massengineer/FYP-ML-Bird-Scarer/train_data_for_fifth_model/train_batch1262.jpg

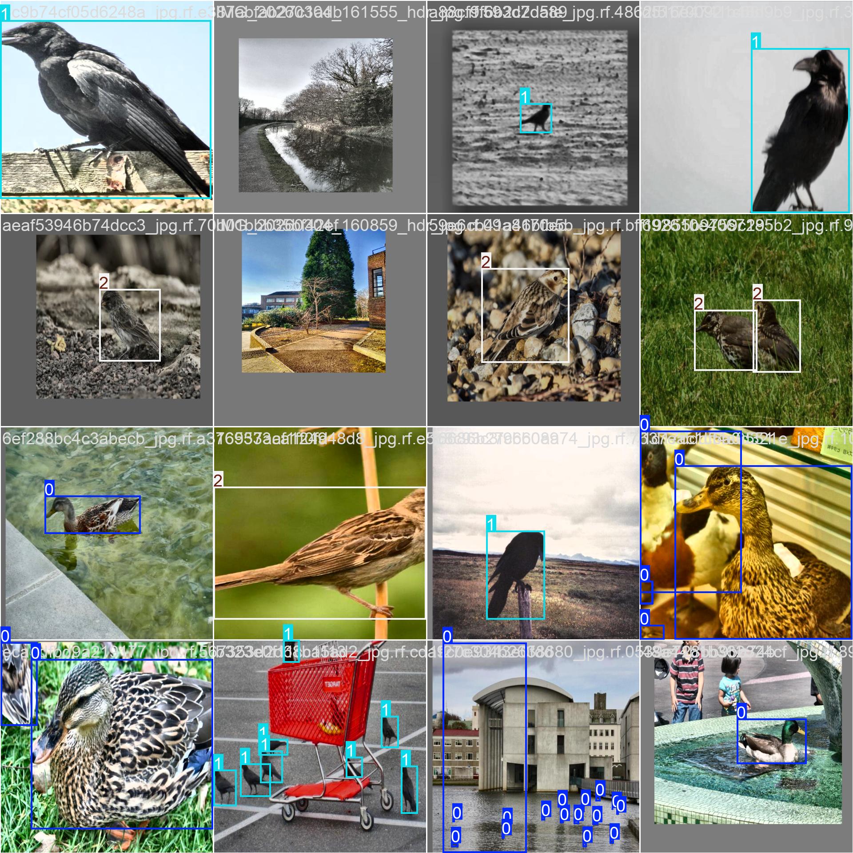
train_data_for_fifth_model/train_batch1262.jpg
