massengineer/FYP-ML-Bird-Scarer/train_data_for_first_model/train_batch451.jpg

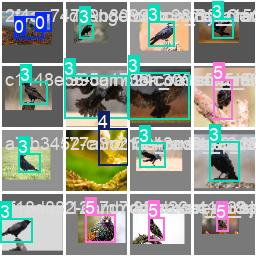
train_data_for_first_model/train_batch451.jpg
