massengineer/FYP-ML-Bird-Scarer/train_data_for_first_model/train_batch452.jpg

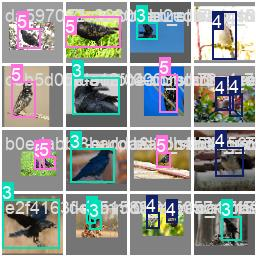
train_data_for_first_model/train_batch452.jpg
