massengineer/FYP-ML-Bird-Scarer/train_data_for_second_model/train_batch12731.jpg

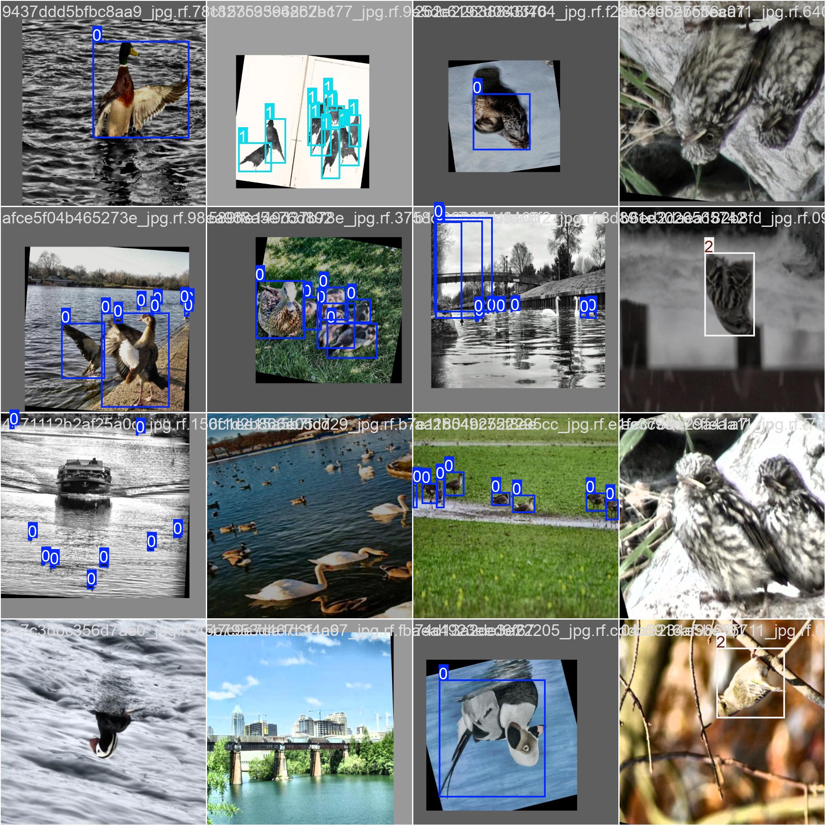
train_data_for_second_model/train_batch12731.jpg
