massengineer/FYP-ML-Bird-Scarer/train_data_for_second_model/val_batch2_labels.jpg

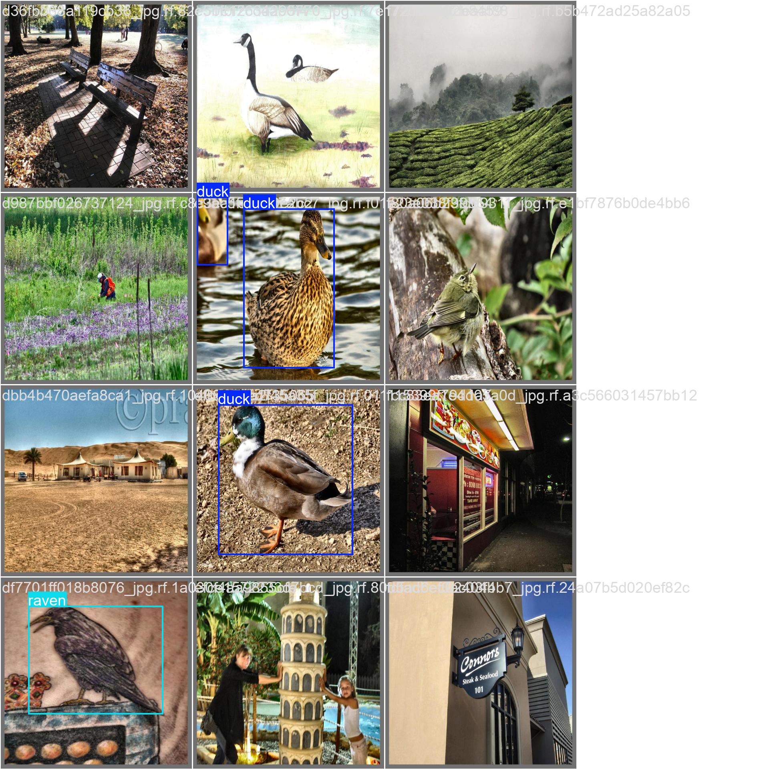
train_data_for_second_model/val_batch2_labels.jpg
