massengineer/FYP-ML-Bird-Scarer/train_data_for_sixth_model/BoxF1_curve.png

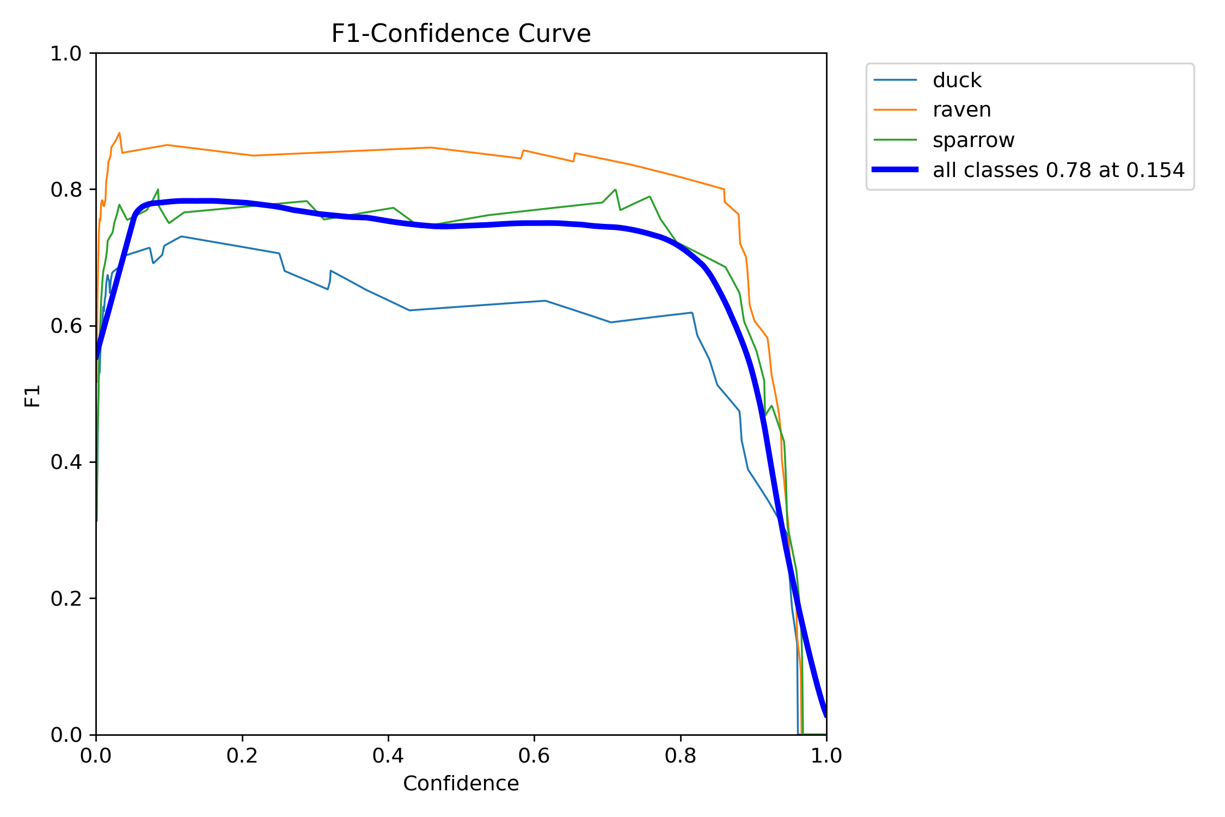
train_data_for_sixth_model/BoxF1_curve.png
