massengineer/FYP-ML-Bird-Scarer/train_data_for_sixth_model/confusion_matrix.png

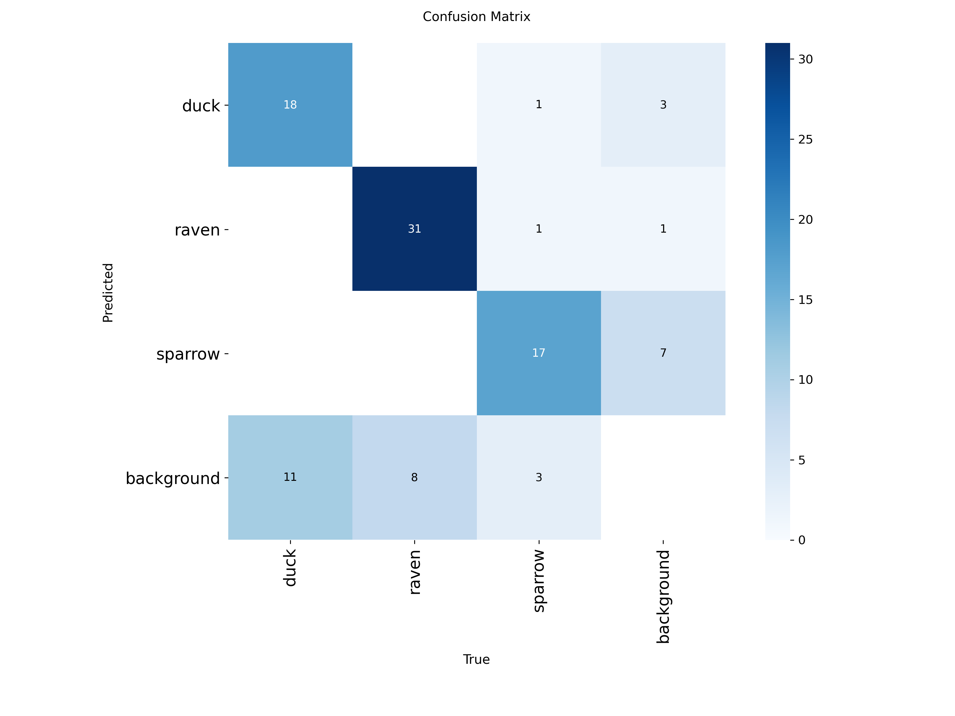
train_data_for_sixth_model/confusion_matrix.png
