massengineer/FYP-ML-Bird-Scarer/train_data_for_sixth_model/confusion_matrix_normalized.png

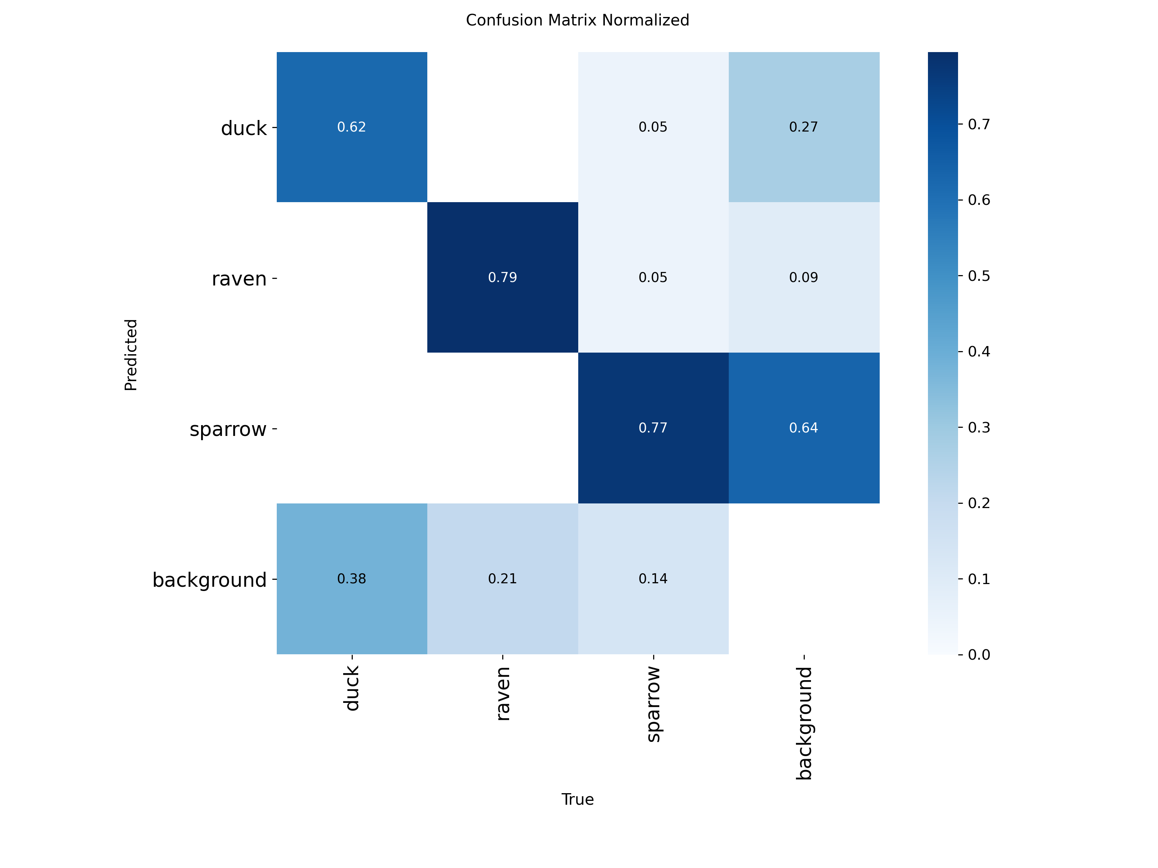
train_data_for_sixth_model/confusion_matrix_normalized.png
