massengineer/FYP-ML-Bird-Scarer/train_data_for_sixth_model/labels.jpg

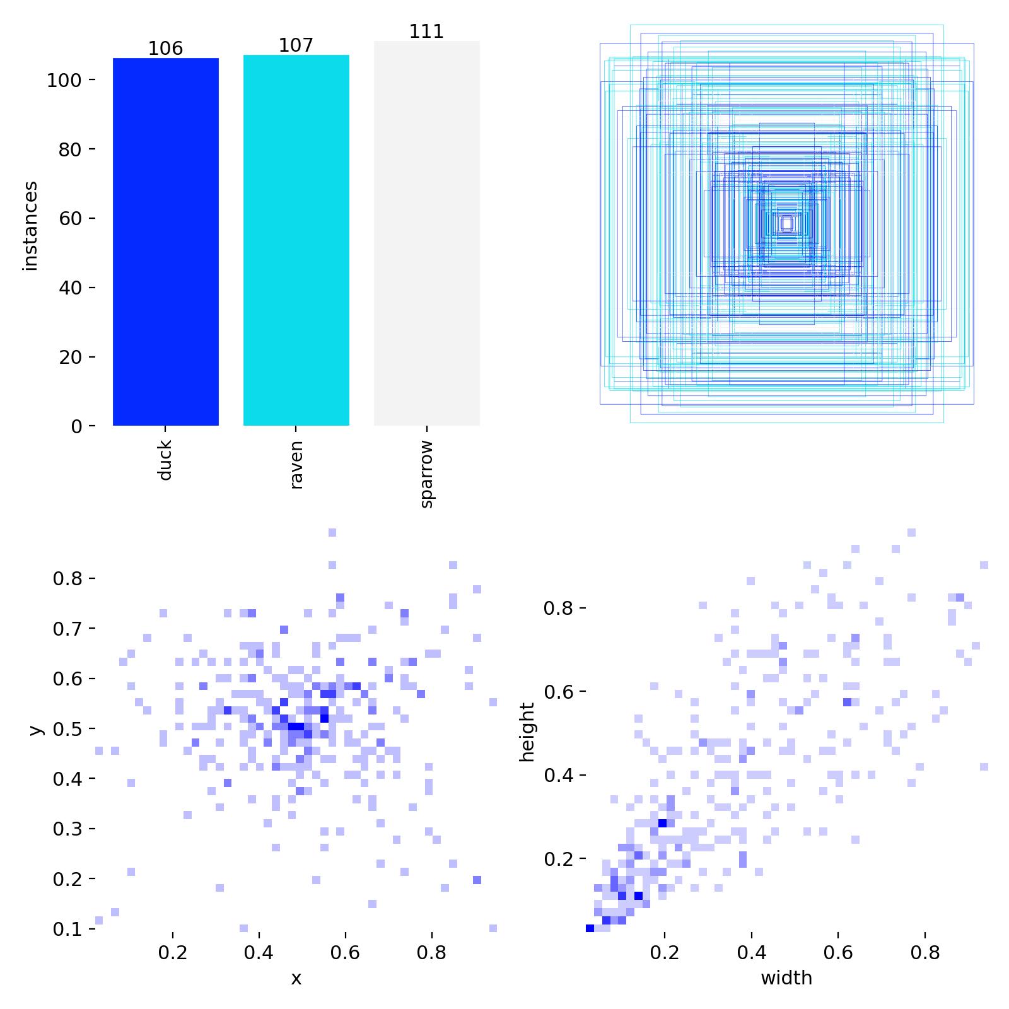
train_data_for_sixth_model/labels.jpg
