massengineer/FYP-ML-Bird-Scarer/train_data_for_sixth_model/train_batch1122.jpg

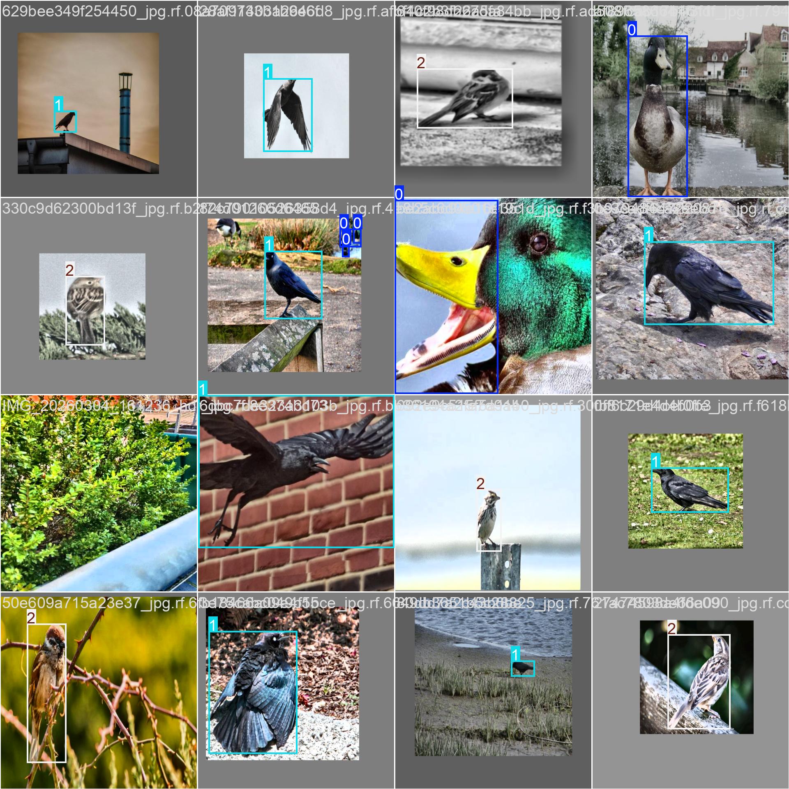
train_data_for_sixth_model/train_batch1122.jpg
