massengineer/FYP-ML-Bird-Scarer/train_data_for_sixth_model/val_batch1_labels.jpg

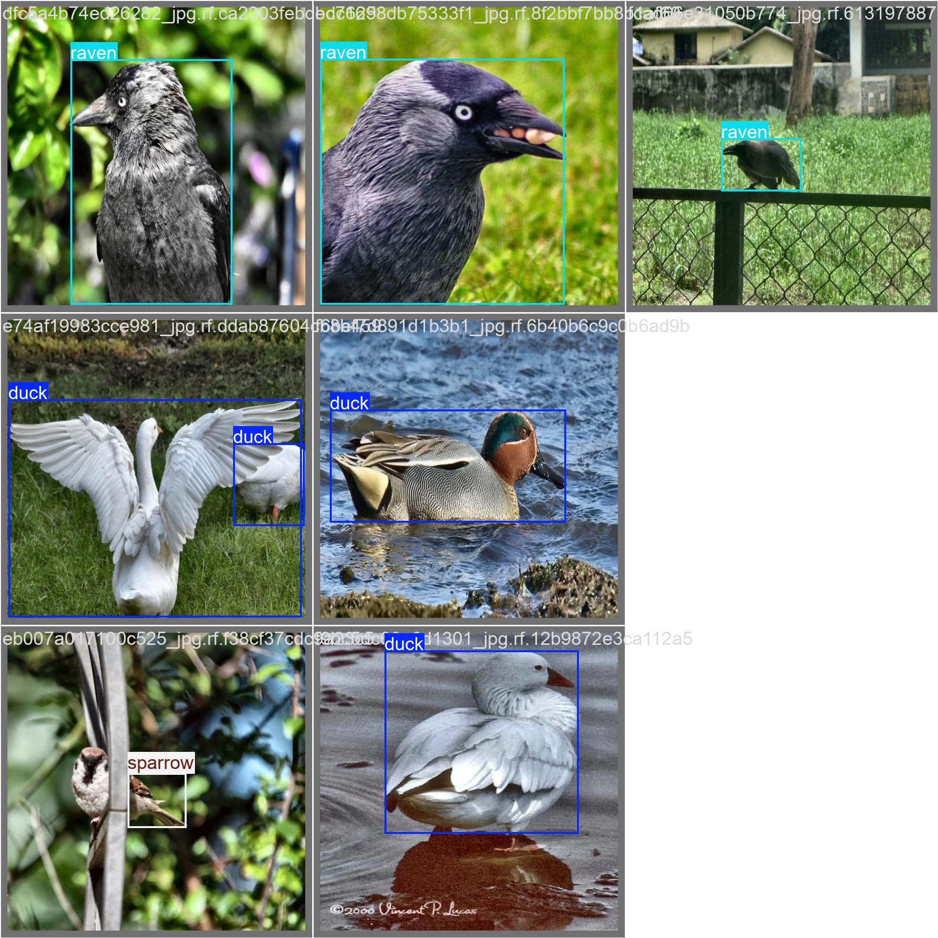
train_data_for_sixth_model/val_batch1_labels.jpg
