massengineer/FYP-ML-Bird-Scarer/train_data_for_third_model/train_batch13490.jpg

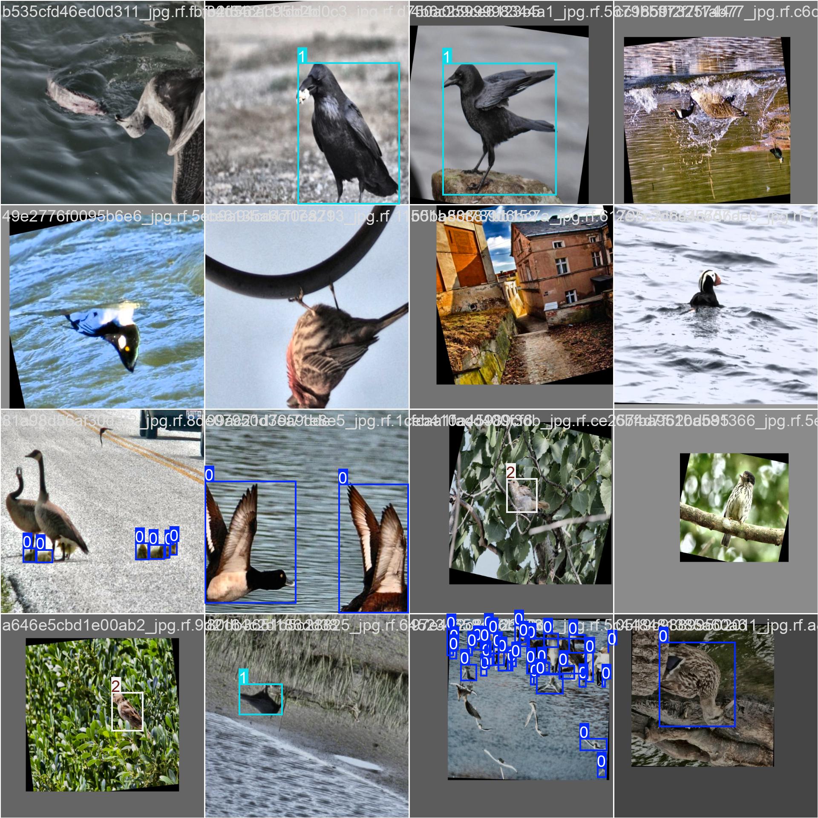
train_data_for_third_model/train_batch13490.jpg
