massengineer/FYP-ML-Bird-Scarer/train_data_for_third_model/train_batch13491.jpg

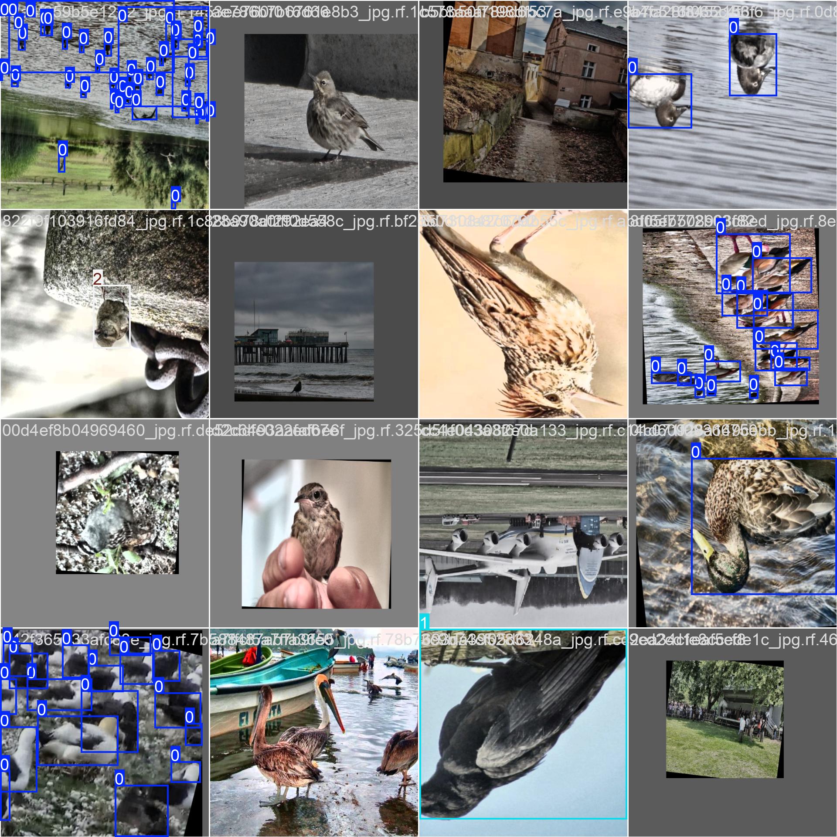
train_data_for_third_model/train_batch13491.jpg
