massengineer/FYP-ML-Bird-Scarer/train_data_for_third_model/train_batch13492.jpg

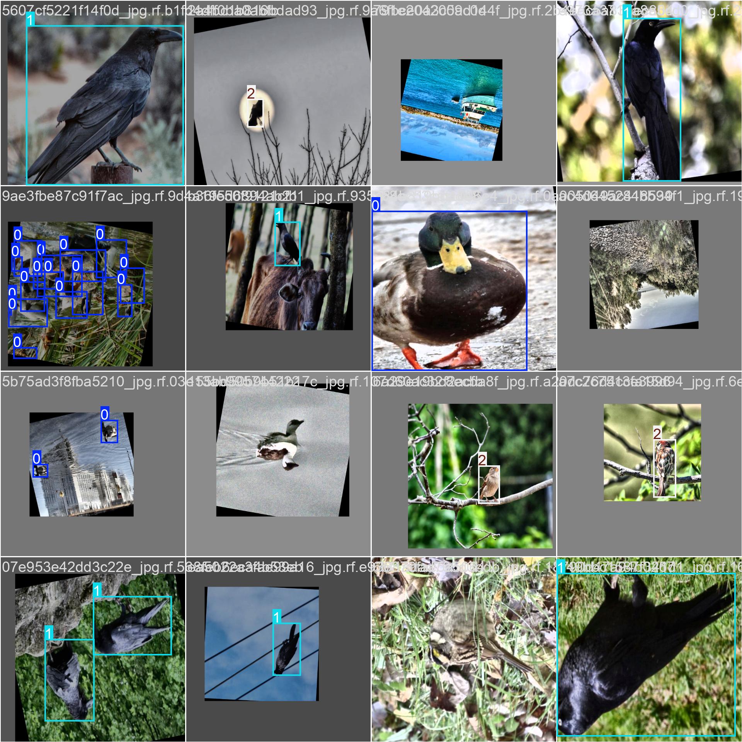
train_data_for_third_model/train_batch13492.jpg
