massengineer/FYP-ML-Bird-Scarer/train_data_for_third_model/val_batch2_labels.jpg

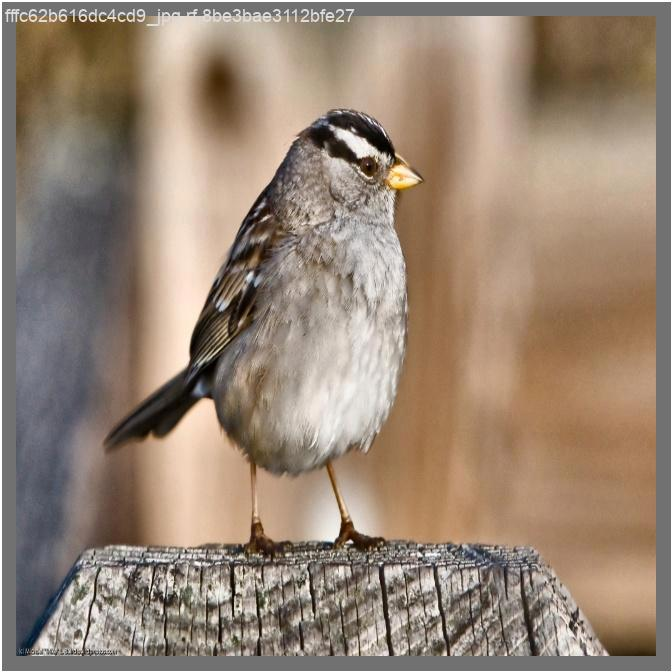
train_data_for_third_model/val_batch2_labels.jpg
