massengineer/FYP-ML-Bird-Scarer/yolo_datasets/raw_datasets/raw_backgrounds_for_fourth_model/IMG_20260304_160844_hdr.jpg

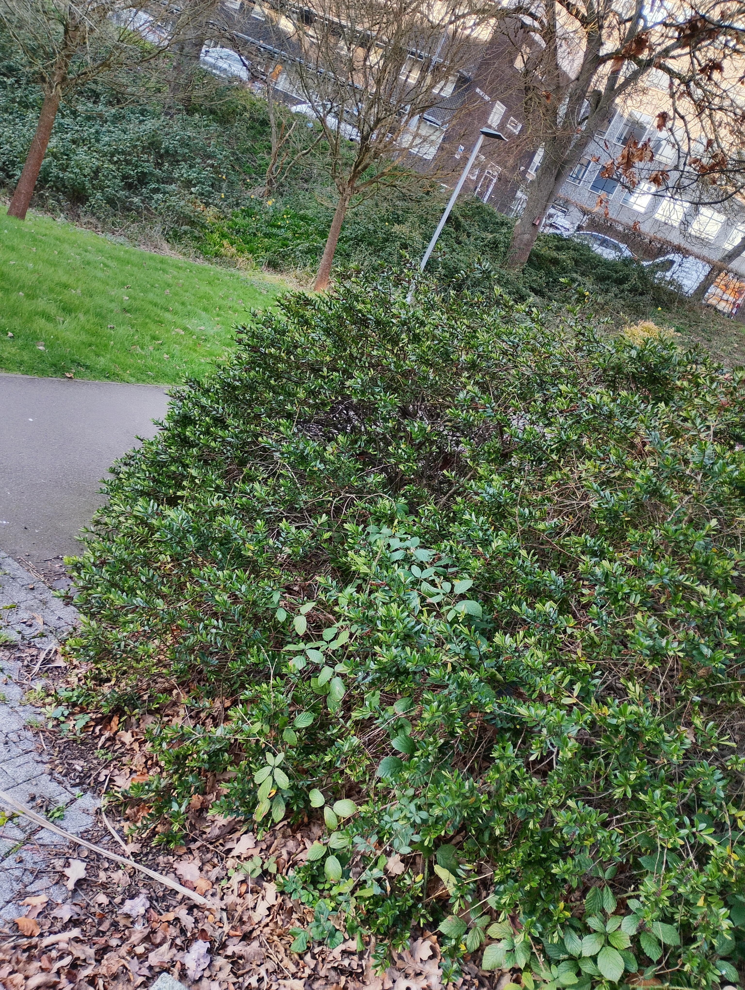
yolo_datasets/raw_datasets/raw_backgrounds_for_fourth_model/IMG_20260304_160844_hdr.jpg
