massengineer/FYP-ML-Bird-Scarer/fifth_model_validation_images/images/0be64d0484da7f5d_jpg.rf.04b6d1586df6ac3ba64640923855f992.jpg

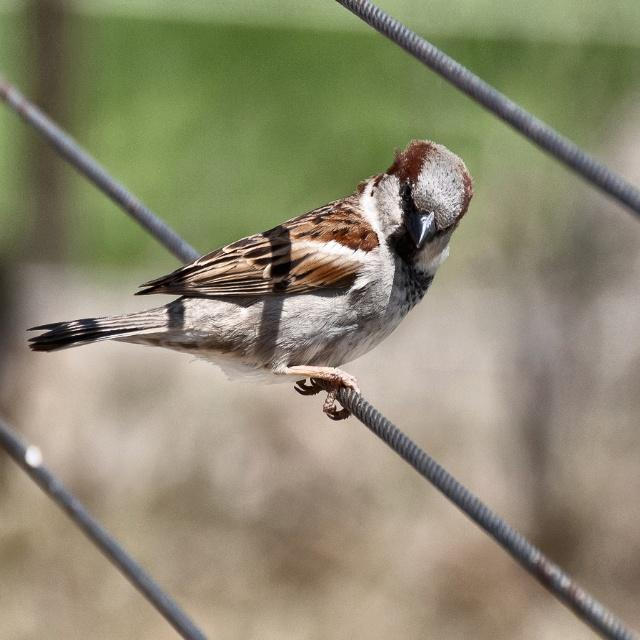
fifth_model_validation_images/images/0be64d0484da7f5d_jpg.rf.04b6d1586df6ac3ba64640923855f992.jpg
