massengineer/FYP-ML-Bird-Scarer/fifth_model_validation_images/images/0de4b4a7943ed37f_jpg.rf.b9594d37234d768218a4663b704f7083.jpg

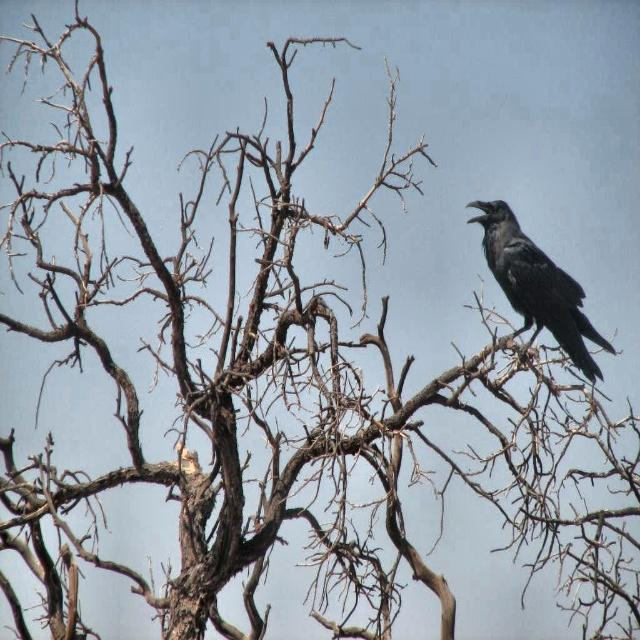
fifth_model_validation_images/images/0de4b4a7943ed37f_jpg.rf.b9594d37234d768218a4663b704f7083.jpg
