massengineer/FYP-ML-Bird-Scarer/fifth_model_validation_images/images/0f1b6b456ff8cd9d_jpg.rf.248c24bbcdb2682d79712362b7e4eebd.jpg

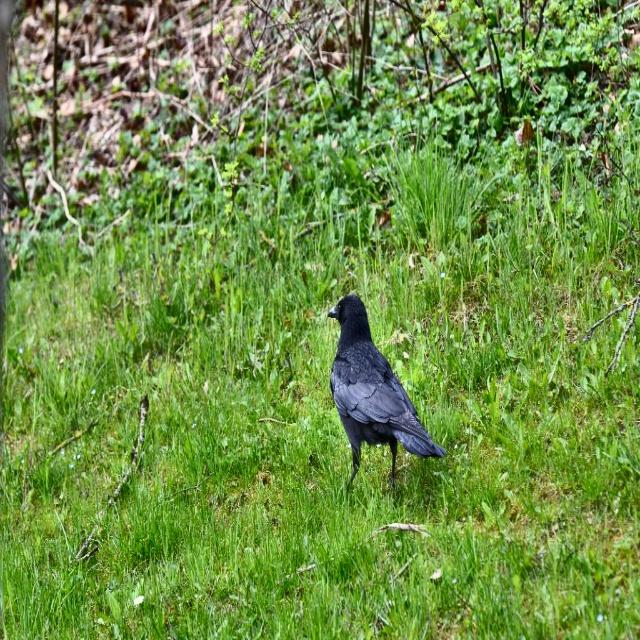
fifth_model_validation_images/images/0f1b6b456ff8cd9d_jpg.rf.248c24bbcdb2682d79712362b7e4eebd.jpg
