massengineer/FYP-ML-Bird-Scarer/fifth_model_validation_images/images/1dcef06e49ea7a7c_jpg.rf.42e672c7e4f9906fecd4efd1ddf9af88.jpg

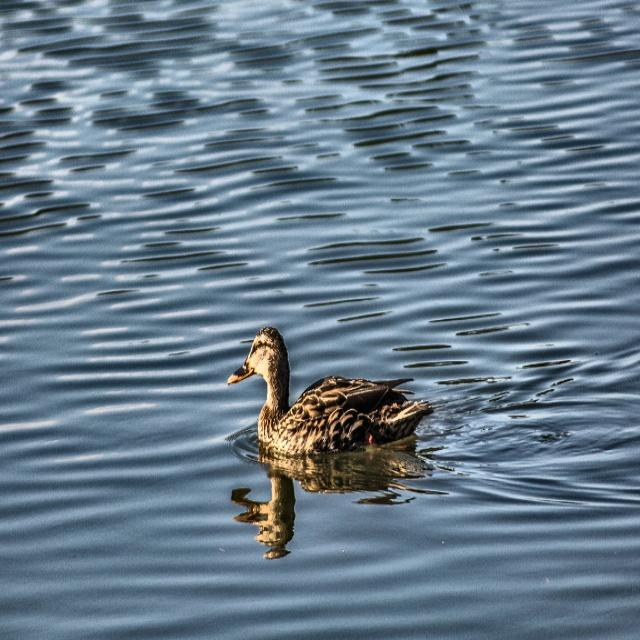
fifth_model_validation_images/images/1dcef06e49ea7a7c_jpg.rf.42e672c7e4f9906fecd4efd1ddf9af88.jpg
