massengineer/FYP-ML-Bird-Scarer/fifth_model_validation_images/images/2b569ea590ce1db2_jpg.rf.67d2292251b5af2b555186cf5ea705ad.jpg

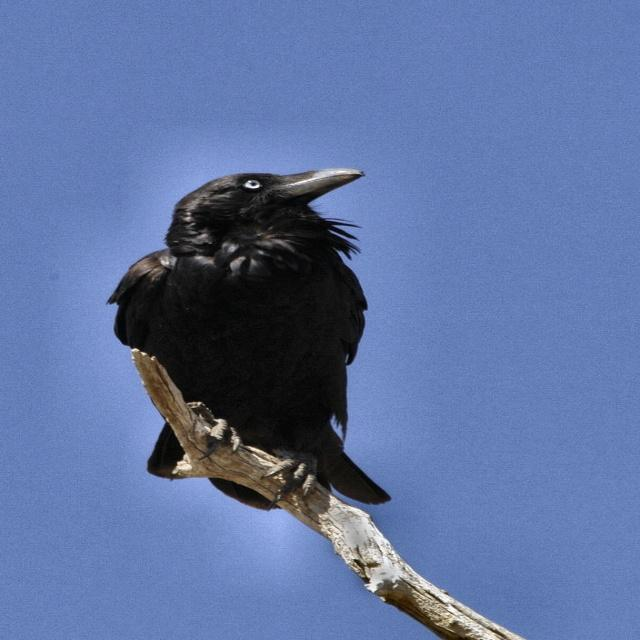
fifth_model_validation_images/images/2b569ea590ce1db2_jpg.rf.67d2292251b5af2b555186cf5ea705ad.jpg
