massengineer/FYP-ML-Bird-Scarer/fifth_model_validation_images/images/2d2721cced07626c_jpg.rf.696016c7bf0ef4f652db7f2fa16d3ebe.jpg

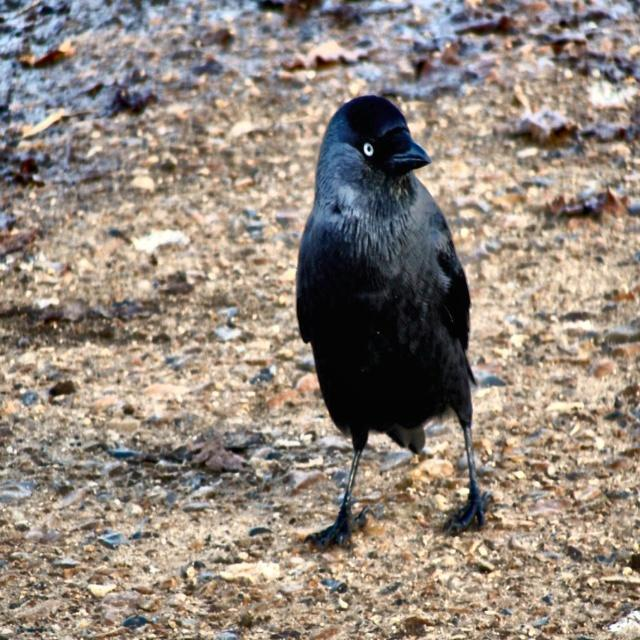
fifth_model_validation_images/images/2d2721cced07626c_jpg.rf.696016c7bf0ef4f652db7f2fa16d3ebe.jpg
