massengineer/FYP-ML-Bird-Scarer/fifth_model_validation_images/images/2de9d305609b8cc4_jpg.rf.c2fc4baab4b9f6159f9ddb58a70e6da2.jpg

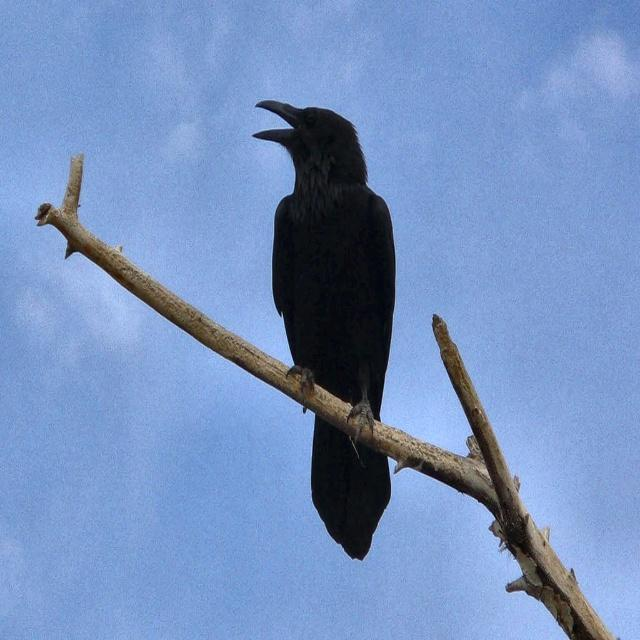
fifth_model_validation_images/images/2de9d305609b8cc4_jpg.rf.c2fc4baab4b9f6159f9ddb58a70e6da2.jpg
