massengineer/FYP-ML-Bird-Scarer/fifth_model_validation_images/images/3c0b50f20b9cccb5_jpg.rf.caedc038e160330f41f902fb228554f5.jpg

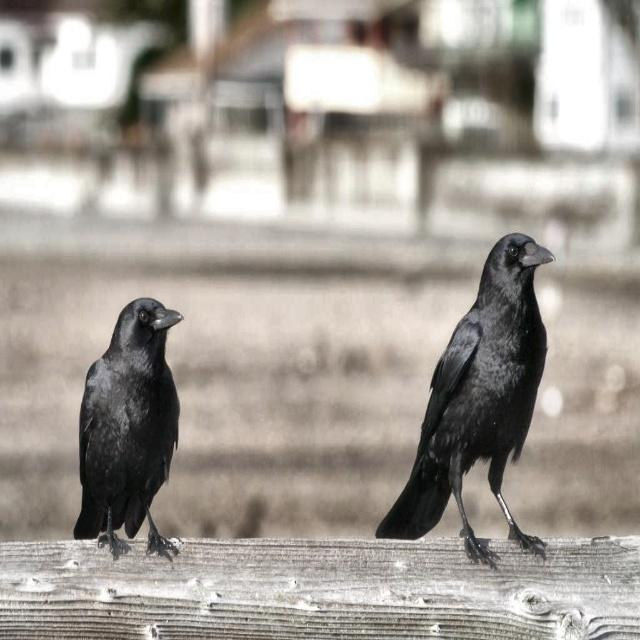
fifth_model_validation_images/images/3c0b50f20b9cccb5_jpg.rf.caedc038e160330f41f902fb228554f5.jpg
