massengineer/FYP-ML-Bird-Scarer/fifth_model_validation_images/images/3c9103fa934be876_jpg.rf.1b80672a4a2a1a34eb28aad57273ca6f.jpg

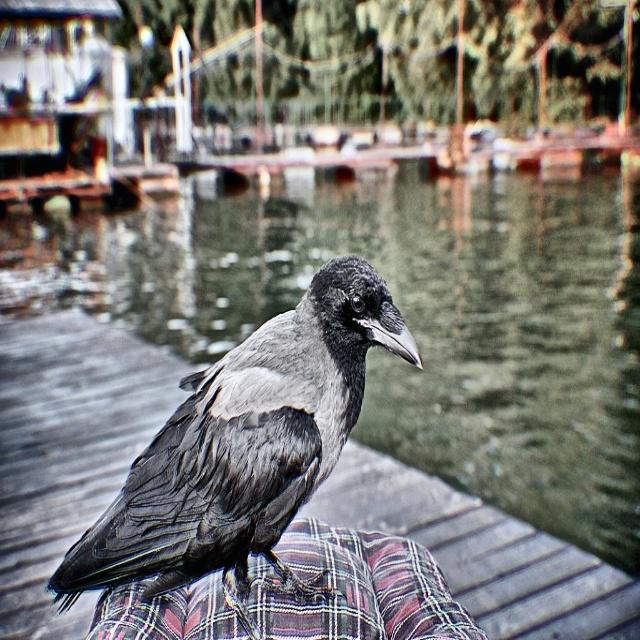
fifth_model_validation_images/images/3c9103fa934be876_jpg.rf.1b80672a4a2a1a34eb28aad57273ca6f.jpg
