massengineer/FYP-ML-Bird-Scarer/fifth_model_validation_images/images/3ce8491f37576abe_jpg.rf.4be57851d7a430a2213e9c7240d35ce1.jpg

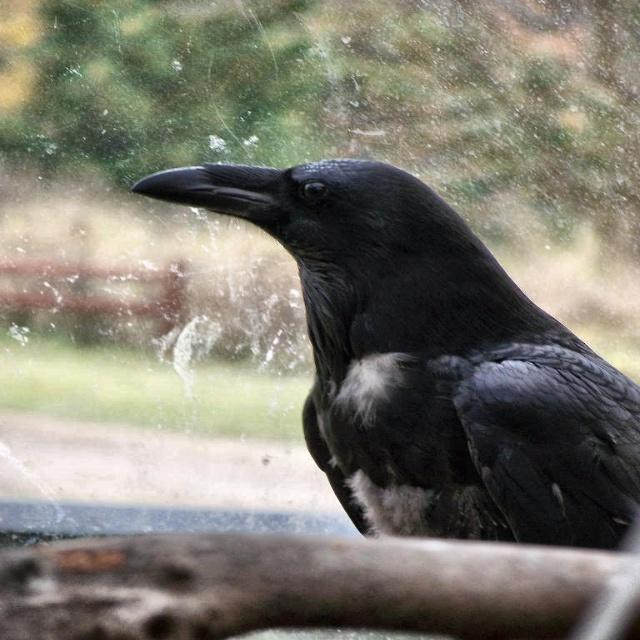
fifth_model_validation_images/images/3ce8491f37576abe_jpg.rf.4be57851d7a430a2213e9c7240d35ce1.jpg
