massengineer/FYP-ML-Bird-Scarer/fifth_model_validation_images/images/4ac98103f6902418_jpg.rf.f355e2eece73f3efba47b437c8df5437.jpg

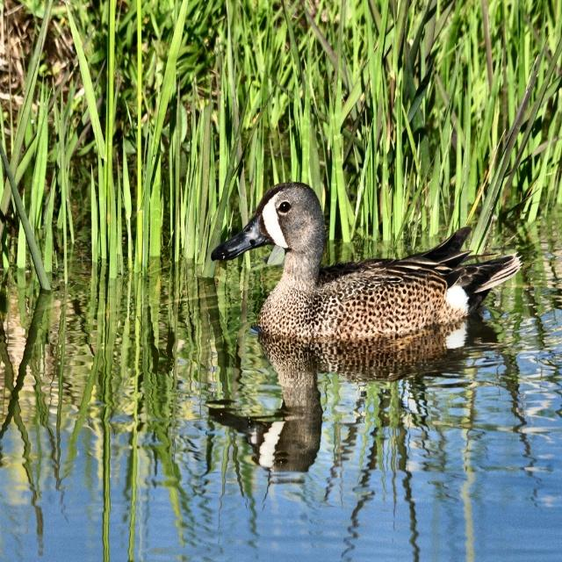
fifth_model_validation_images/images/4ac98103f6902418_jpg.rf.f355e2eece73f3efba47b437c8df5437.jpg
