massengineer/FYP-ML-Bird-Scarer/fifth_model_validation_images/images/4cb8bc5a7666f66f_jpg.rf.4776c85a03ee199fc77abfe076986128.jpg

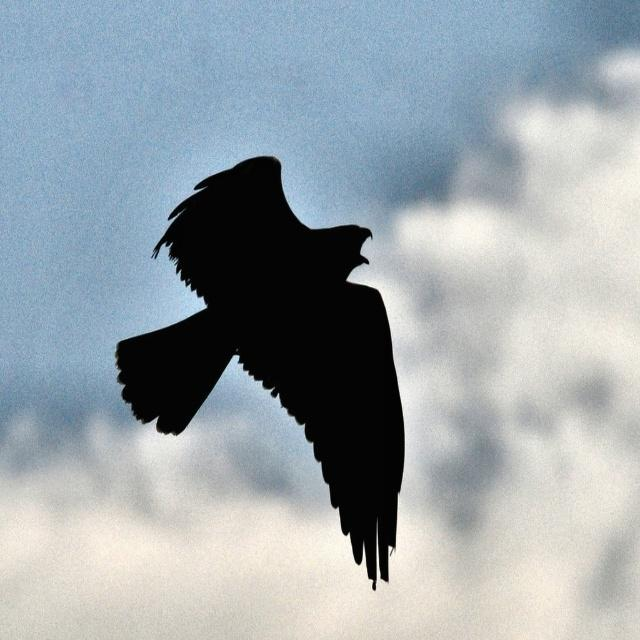
fifth_model_validation_images/images/4cb8bc5a7666f66f_jpg.rf.4776c85a03ee199fc77abfe076986128.jpg
