massengineer/FYP-ML-Bird-Scarer/fifth_model_validation_images/images/4effb07ed2c22bd3_jpg.rf.99be9b13471a686662674c35d63af22f.jpg

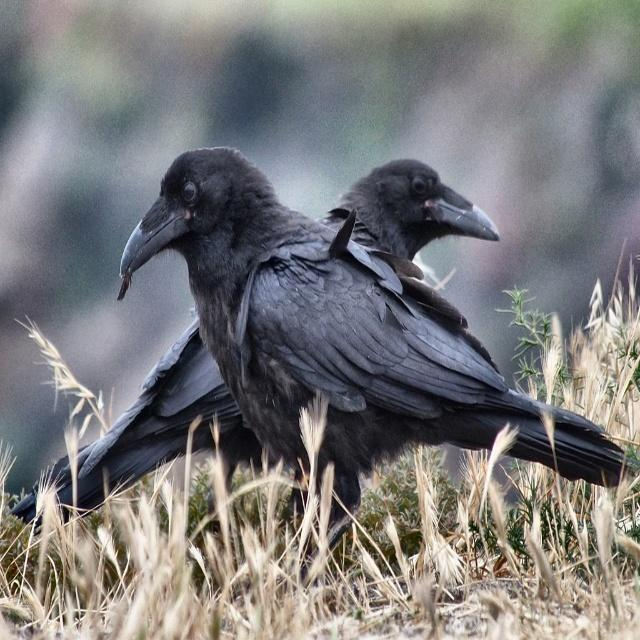
fifth_model_validation_images/images/4effb07ed2c22bd3_jpg.rf.99be9b13471a686662674c35d63af22f.jpg
