massengineer/FYP-ML-Bird-Scarer/fifth_model_validation_images/images/5e3f348764a5eef8_jpg.rf.422f0adb134aaac1838261bf152511c6.jpg

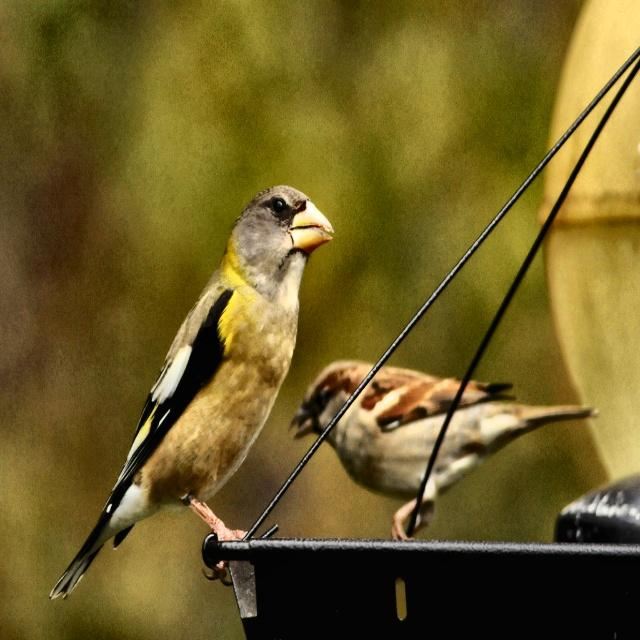
fifth_model_validation_images/images/5e3f348764a5eef8_jpg.rf.422f0adb134aaac1838261bf152511c6.jpg
