massengineer/FYP-ML-Bird-Scarer/fifth_model_validation_images/images/5fa36b7ab3f99b57_jpg.rf.4fb009745905087155a14afa6f6e8ed5.jpg

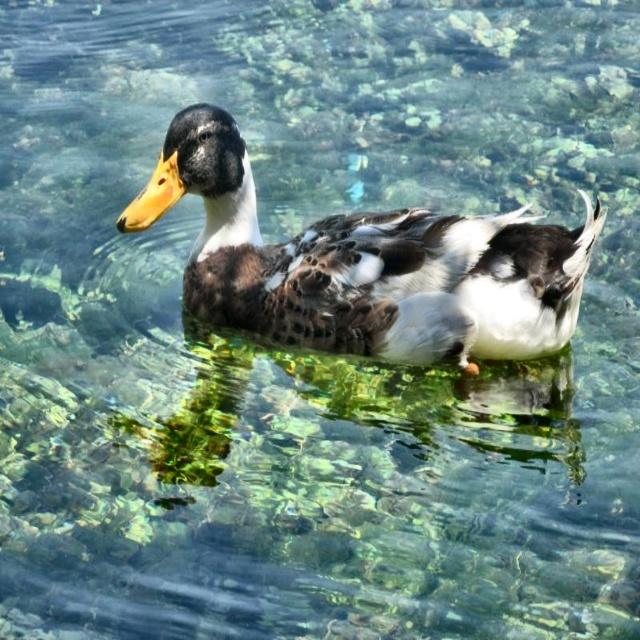
fifth_model_validation_images/images/5fa36b7ab3f99b57_jpg.rf.4fb009745905087155a14afa6f6e8ed5.jpg
