massengineer/FYP-ML-Bird-Scarer/fifth_model_validation_images/images/7e1ffb219a2a522b_jpg.rf.1393dfc984291c2c9076b45750de1e1d.jpg

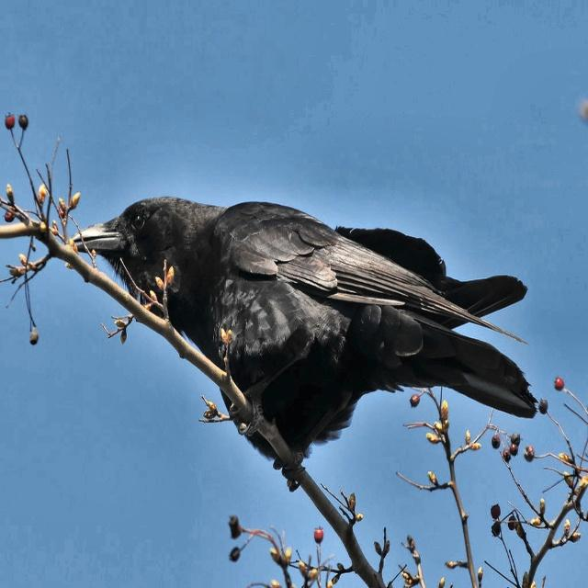
fifth_model_validation_images/images/7e1ffb219a2a522b_jpg.rf.1393dfc984291c2c9076b45750de1e1d.jpg
