massengineer/FYP-ML-Bird-Scarer/fifth_model_validation_images/images/8bce0ef025411ed1_jpg.rf.2814e396186e43bf01ed99291d027d92.jpg

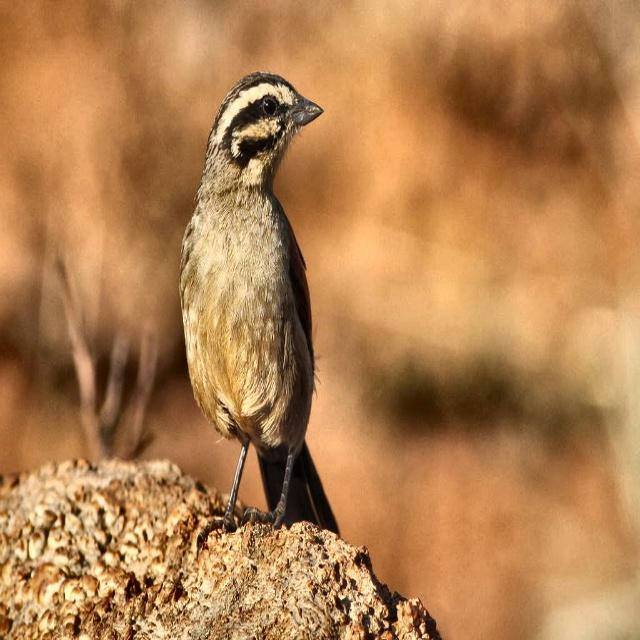
fifth_model_validation_images/images/8bce0ef025411ed1_jpg.rf.2814e396186e43bf01ed99291d027d92.jpg
