massengineer/FYP-ML-Bird-Scarer/fifth_model_validation_images/images/9bb2d29bb96724c6_jpg.rf.1a6e348eabfad239e67b68433f5f388f.jpg

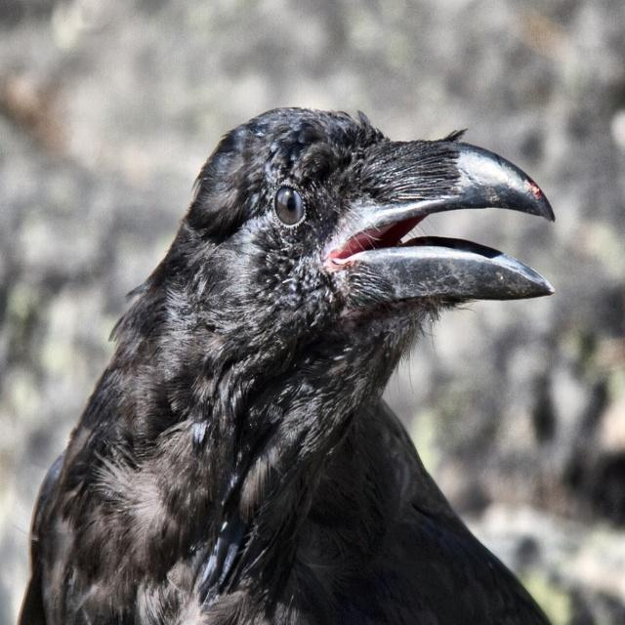
fifth_model_validation_images/images/9bb2d29bb96724c6_jpg.rf.1a6e348eabfad239e67b68433f5f388f.jpg
