massengineer/FYP-ML-Bird-Scarer/fifth_model_validation_images/images/9f813f146b94f087_jpg.rf.ed6a436854f7ce6db7ea7519b66a86ef.jpg

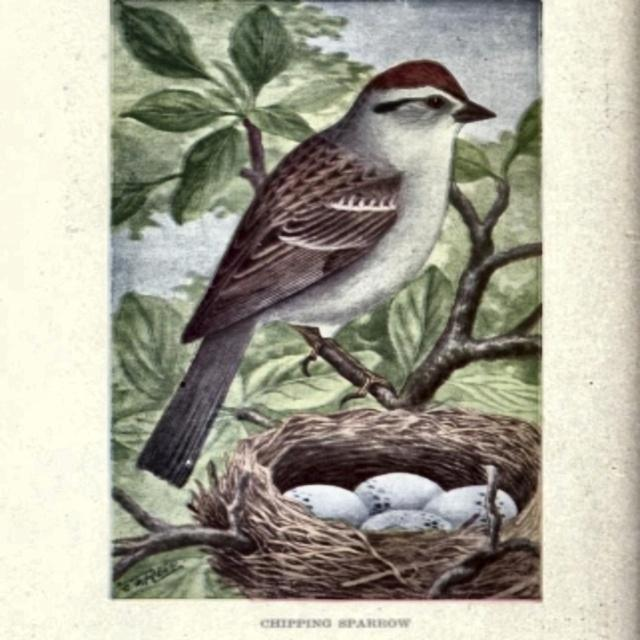
fifth_model_validation_images/images/9f813f146b94f087_jpg.rf.ed6a436854f7ce6db7ea7519b66a86ef.jpg
