massengineer/FYP-ML-Bird-Scarer/fifth_model_validation_images/images/22aa6924c696b9df_jpg.rf.54d9e55d646cb2611108bd9d270b6c9e.jpg

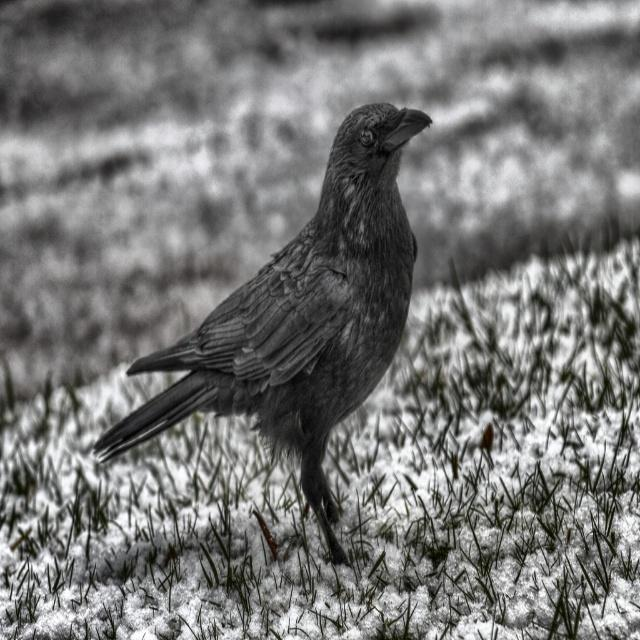
fifth_model_validation_images/images/22aa6924c696b9df_jpg.rf.54d9e55d646cb2611108bd9d270b6c9e.jpg
