massengineer/FYP-ML-Bird-Scarer/fifth_model_validation_images/images/24cab1cdcadd2906_jpg.rf.8a631ed6f84598b9b1aee93e4d02c651.jpg

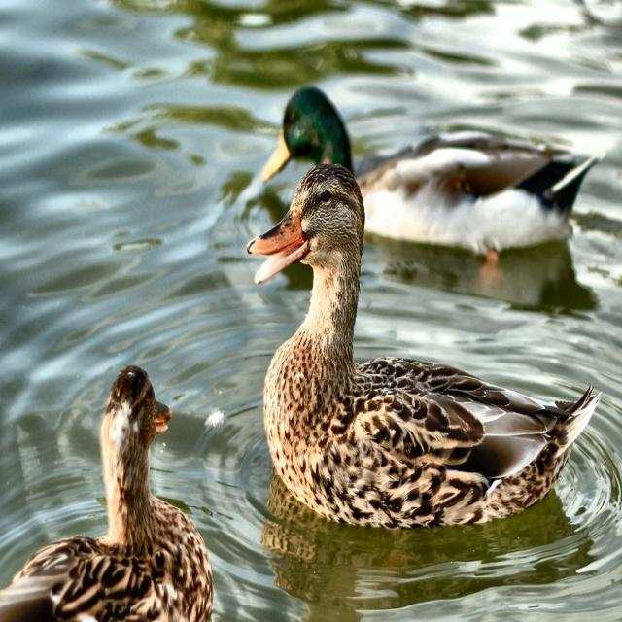
fifth_model_validation_images/images/24cab1cdcadd2906_jpg.rf.8a631ed6f84598b9b1aee93e4d02c651.jpg
