massengineer/FYP-ML-Bird-Scarer/fifth_model_validation_images/images/057f0de7e671b75c_jpg.rf.2dd9f41e60b7a2de076f6edf6c3f98c5.jpg

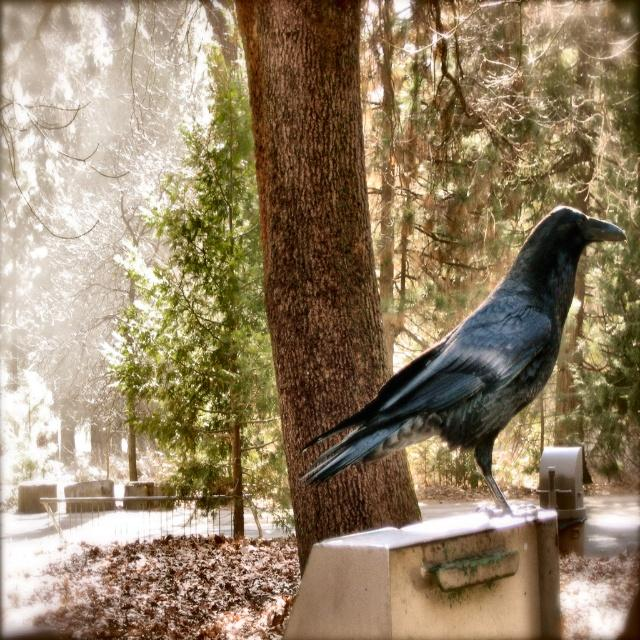
fifth_model_validation_images/images/057f0de7e671b75c_jpg.rf.2dd9f41e60b7a2de076f6edf6c3f98c5.jpg
