massengineer/FYP-ML-Bird-Scarer/fifth_model_validation_images/images/73a1b642339b4ec0_jpg.rf.175f9d27eda6b595fa8adb0b344427a3.jpg

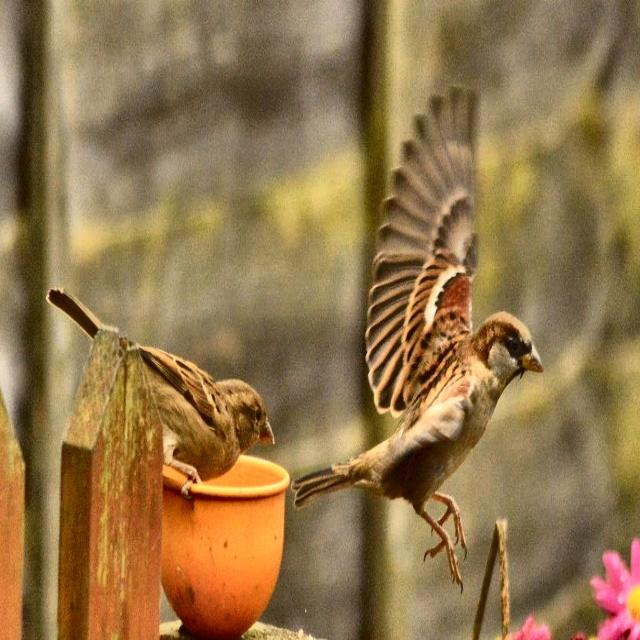
fifth_model_validation_images/images/73a1b642339b4ec0_jpg.rf.175f9d27eda6b595fa8adb0b344427a3.jpg
