massengineer/FYP-ML-Bird-Scarer/fifth_model_validation_images/images/84ef1881685cd206_jpg.rf.76c47fa663c3859b4896b602b45732bb.jpg

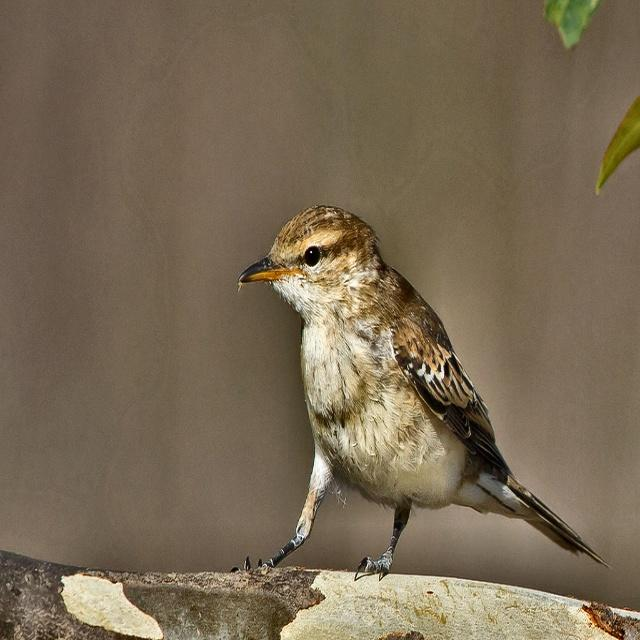
fifth_model_validation_images/images/84ef1881685cd206_jpg.rf.76c47fa663c3859b4896b602b45732bb.jpg
