massengineer/FYP-ML-Bird-Scarer/fifth_model_validation_images/images/93b6f17a0cf6b67b_jpg.rf.c7610ac2f88afec8820649ae66cb56ca.jpg

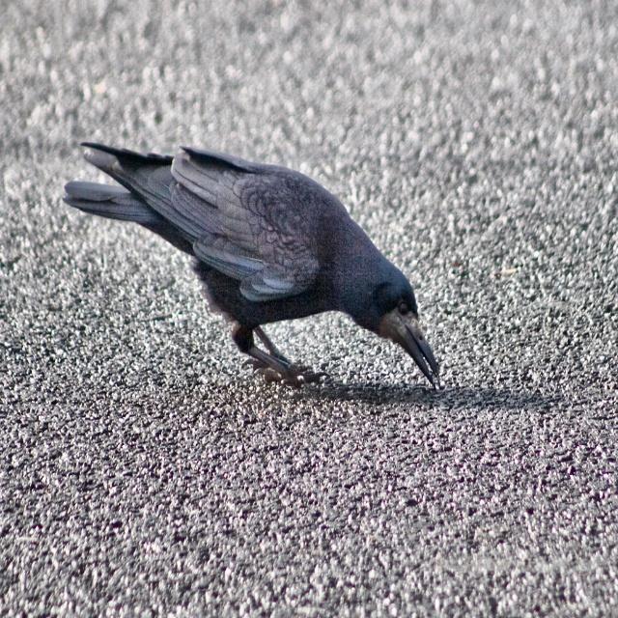
fifth_model_validation_images/images/93b6f17a0cf6b67b_jpg.rf.c7610ac2f88afec8820649ae66cb56ca.jpg
