massengineer/FYP-ML-Bird-Scarer/fifth_model_validation_images/images/94eb81cf26257bfb_jpg.rf.2ae2b793689980e837b499f0b69c3a8b.jpg

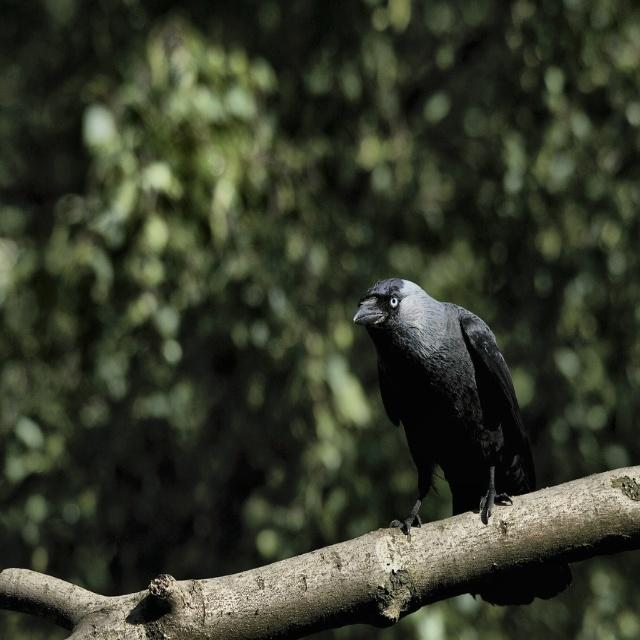
fifth_model_validation_images/images/94eb81cf26257bfb_jpg.rf.2ae2b793689980e837b499f0b69c3a8b.jpg
