massengineer/FYP-ML-Bird-Scarer/fifth_model_validation_images/images/97c735f24d1822c4_jpg.rf.b55590020fa06321282a1aeb94cfc051.jpg

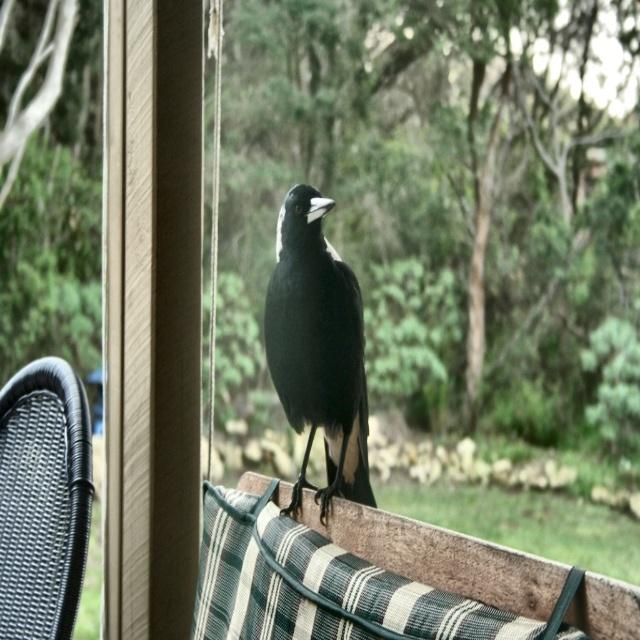
fifth_model_validation_images/images/97c735f24d1822c4_jpg.rf.b55590020fa06321282a1aeb94cfc051.jpg
