massengineer/FYP-ML-Bird-Scarer/fifth_model_validation_images/images/99d4241ec2013bb5_jpg.rf.05ae8fb1f897e008a1f890e7e9f91ab8.jpg

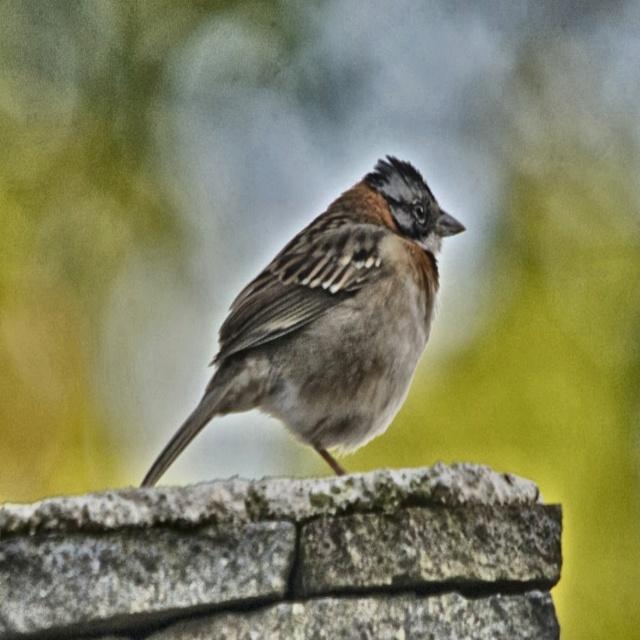
fifth_model_validation_images/images/99d4241ec2013bb5_jpg.rf.05ae8fb1f897e008a1f890e7e9f91ab8.jpg
