massengineer/FYP-ML-Bird-Scarer/fifth_model_validation_images/images/454ffdabe8fc2a90_jpg.rf.b0b41fb94497174f44b9e8e404c59a25.jpg

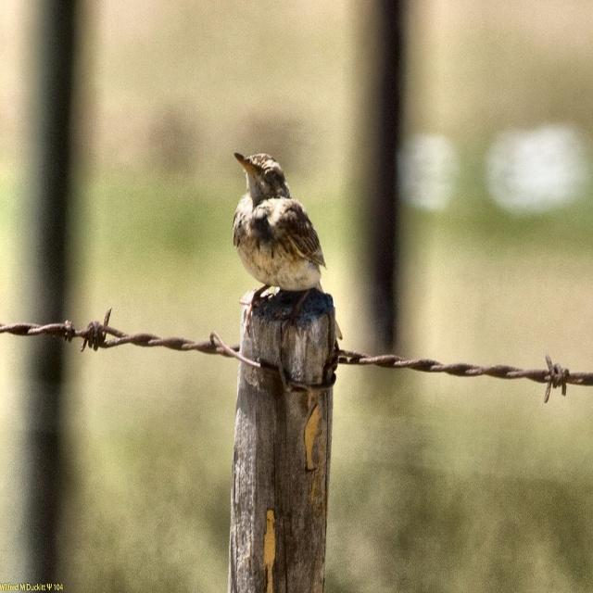
fifth_model_validation_images/images/454ffdabe8fc2a90_jpg.rf.b0b41fb94497174f44b9e8e404c59a25.jpg
