massengineer/FYP-ML-Bird-Scarer/fifth_model_validation_images/images/457cc45bbf76ebd8_jpg.rf.342174bdba511b1fcd8e96f08e92036c.jpg

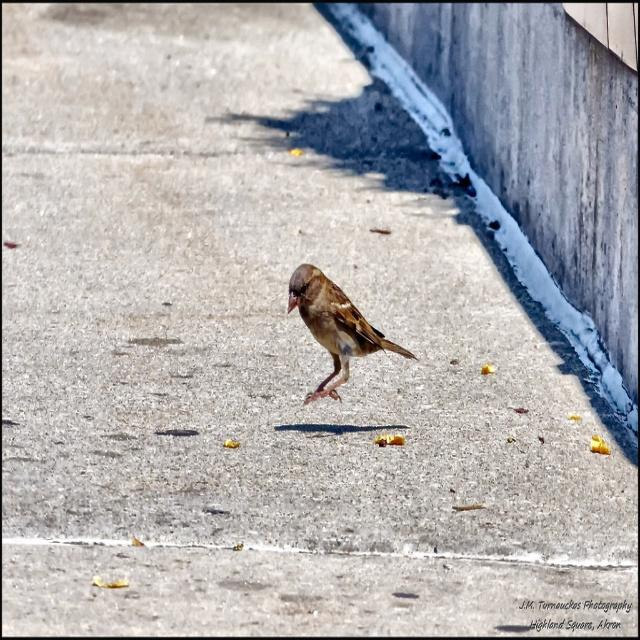
fifth_model_validation_images/images/457cc45bbf76ebd8_jpg.rf.342174bdba511b1fcd8e96f08e92036c.jpg
