massengineer/FYP-ML-Bird-Scarer/fifth_model_validation_images/images/799e4461dfecc042_jpg.rf.c2b996e4ab66f2e8d4488a540541f9b0.jpg

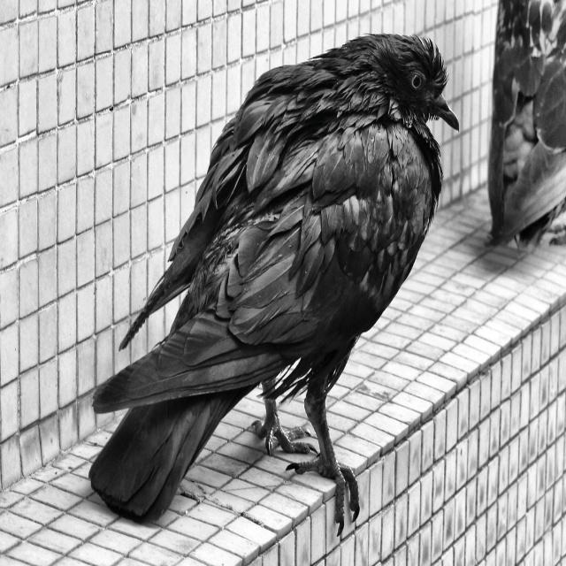
fifth_model_validation_images/images/799e4461dfecc042_jpg.rf.c2b996e4ab66f2e8d4488a540541f9b0.jpg
