massengineer/FYP-ML-Bird-Scarer/fifth_model_validation_images/images/2280dccc29233e2c_jpg.rf.a18d0688116a1611f87abedd1e81104a.jpg

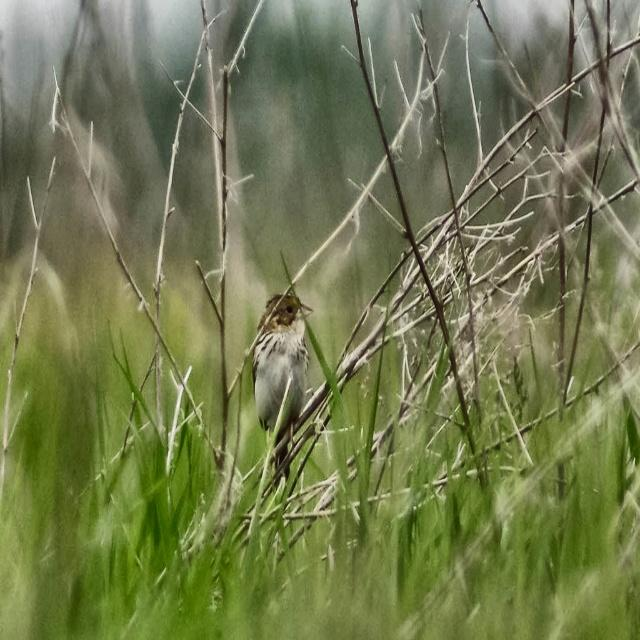
fifth_model_validation_images/images/2280dccc29233e2c_jpg.rf.a18d0688116a1611f87abedd1e81104a.jpg
