massengineer/FYP-ML-Bird-Scarer/fifth_model_validation_images/images/3360d48e343f7778_jpg.rf.2e698647f89db22aace6074f9f631b46.jpg

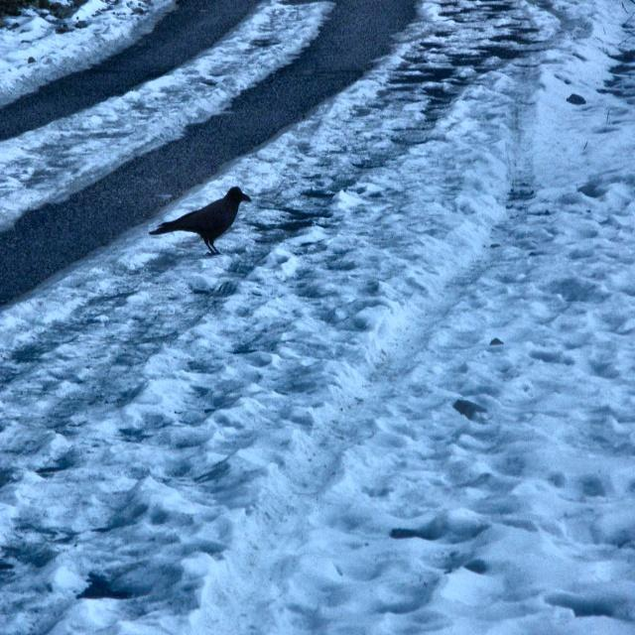
fifth_model_validation_images/images/3360d48e343f7778_jpg.rf.2e698647f89db22aace6074f9f631b46.jpg
