massengineer/FYP-ML-Bird-Scarer/fifth_model_validation_images/images/4646f8462cb157aa_jpg.rf.9807cf82f95843391a81e97fb256e024.jpg

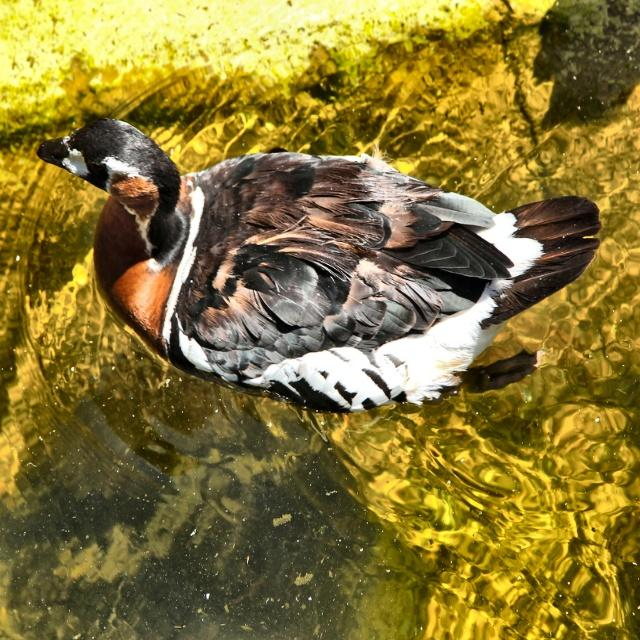
fifth_model_validation_images/images/4646f8462cb157aa_jpg.rf.9807cf82f95843391a81e97fb256e024.jpg
