massengineer/FYP-ML-Bird-Scarer/fifth_model_validation_images/images/5607cf5221f14f0d_jpg.rf.7a0a9b52d251626db6132a9d4003963e.jpg

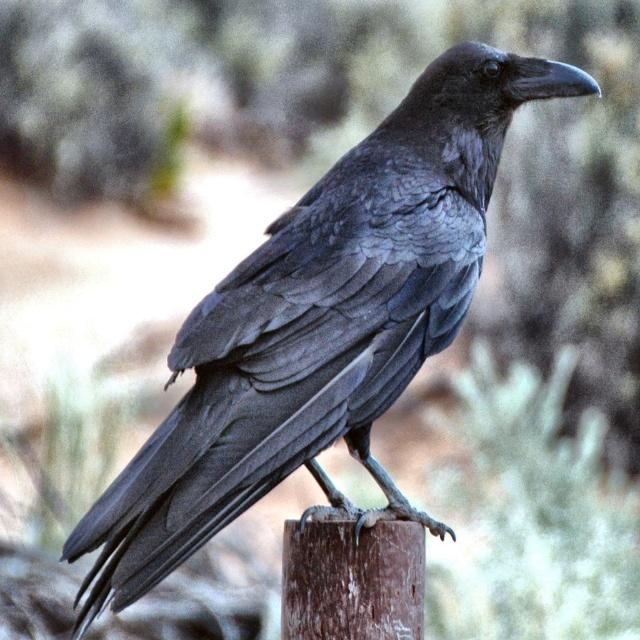
fifth_model_validation_images/images/5607cf5221f14f0d_jpg.rf.7a0a9b52d251626db6132a9d4003963e.jpg
