massengineer/FYP-ML-Bird-Scarer/fifth_model_validation_images/images/37243e86f12f7da9_jpg.rf.5ab5b7b67bfa881676670ea05f2f4506.jpg

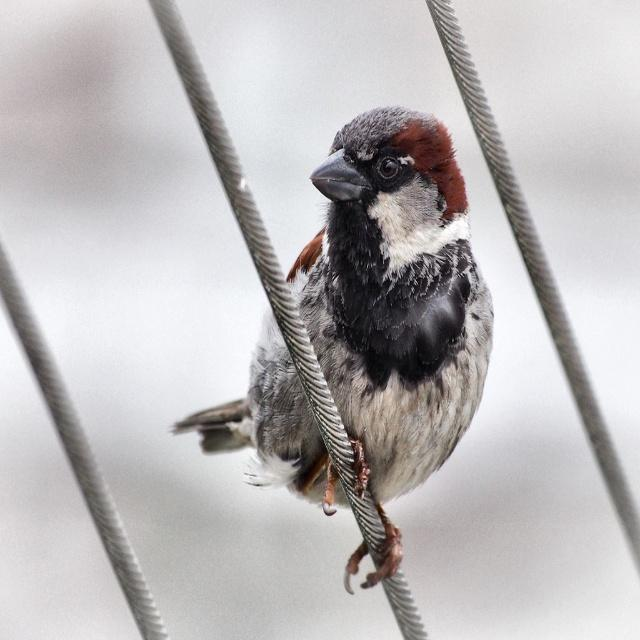
fifth_model_validation_images/images/37243e86f12f7da9_jpg.rf.5ab5b7b67bfa881676670ea05f2f4506.jpg
