massengineer/FYP-ML-Bird-Scarer/fifth_model_validation_images/images/39446c4eb4239a53_jpg.rf.e4ee3d5d9efa6a0450a6b544321e1a87.jpg

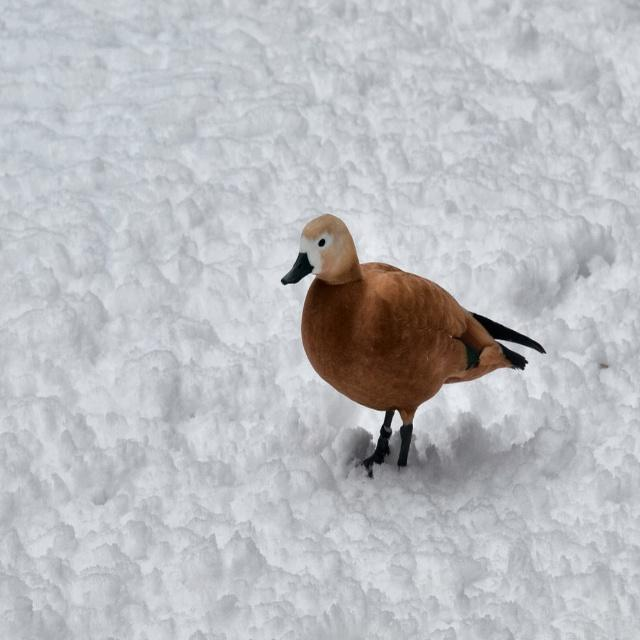
fifth_model_validation_images/images/39446c4eb4239a53_jpg.rf.e4ee3d5d9efa6a0450a6b544321e1a87.jpg
