massengineer/FYP-ML-Bird-Scarer/fifth_model_validation_images/images/88838b028373f49c_jpg.rf.939ac703f508bf58e971c0b2d273a10e.jpg

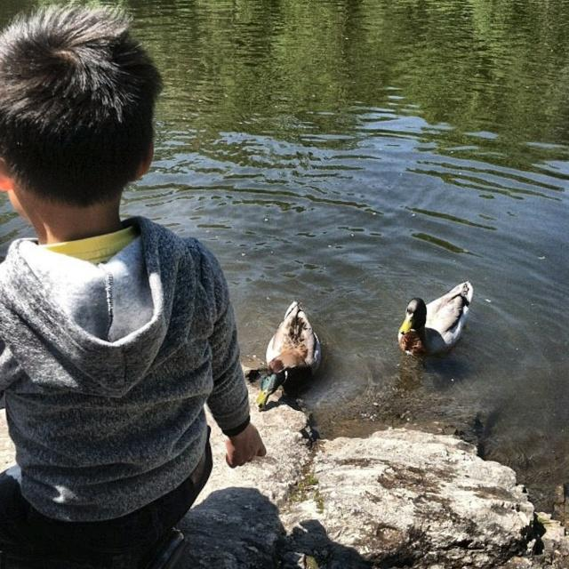
fifth_model_validation_images/images/88838b028373f49c_jpg.rf.939ac703f508bf58e971c0b2d273a10e.jpg
