massengineer/FYP-ML-Bird-Scarer/fifth_model_validation_images/images/2941067e0bf4448d_jpg.rf.8fa182a39cac516869ab31e1cea479f9.jpg

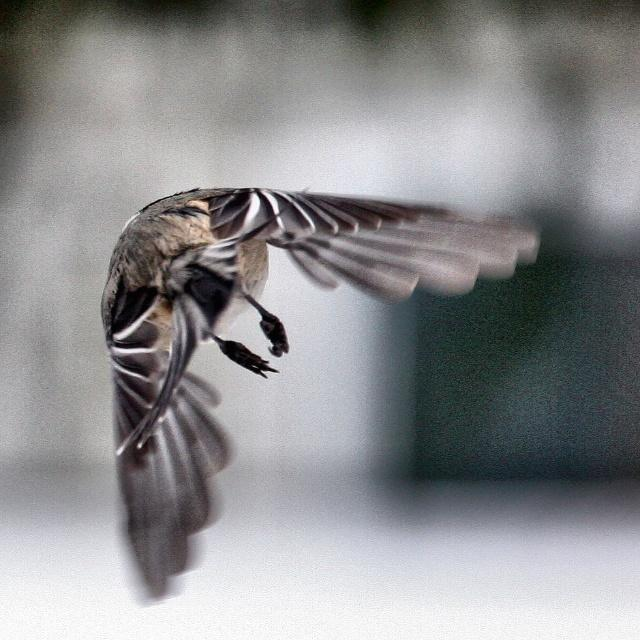
fifth_model_validation_images/images/2941067e0bf4448d_jpg.rf.8fa182a39cac516869ab31e1cea479f9.jpg
