massengineer/FYP-ML-Bird-Scarer/fifth_model_validation_images/images/3638655f6f373a03_jpg.rf.9f16446c2704d9772bb9713dd3f3a15b.jpg

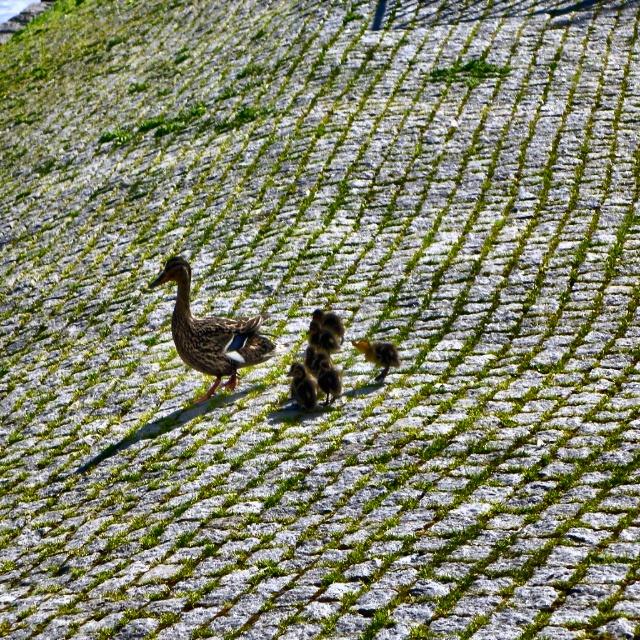
fifth_model_validation_images/images/3638655f6f373a03_jpg.rf.9f16446c2704d9772bb9713dd3f3a15b.jpg
