massengineer/FYP-ML-Bird-Scarer/fifth_model_validation_images/images/7700779ccf7fa900_jpg.rf.c99bd053435c66ea0b4e6bdd7bd4ff6e.jpg

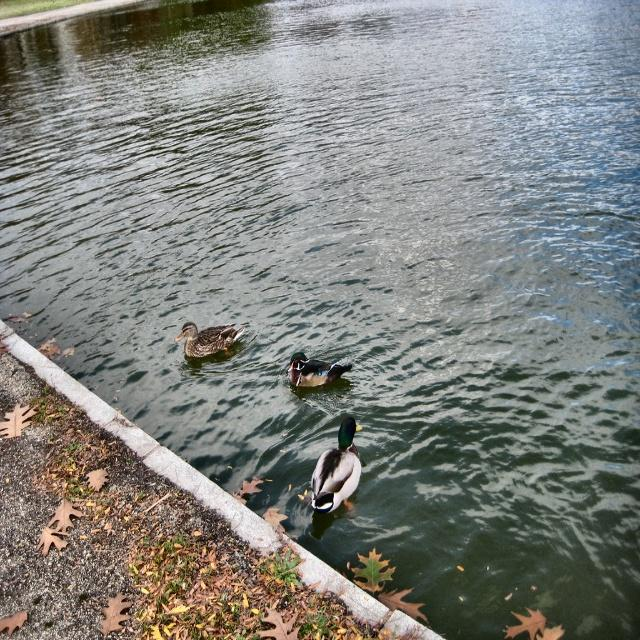
fifth_model_validation_images/images/7700779ccf7fa900_jpg.rf.c99bd053435c66ea0b4e6bdd7bd4ff6e.jpg
