massengineer/FYP-ML-Bird-Scarer/fifth_model_validation_images/images/34544401c4a3e79f_jpg.rf.0eca268f61210abd825abad05dea3782.jpg

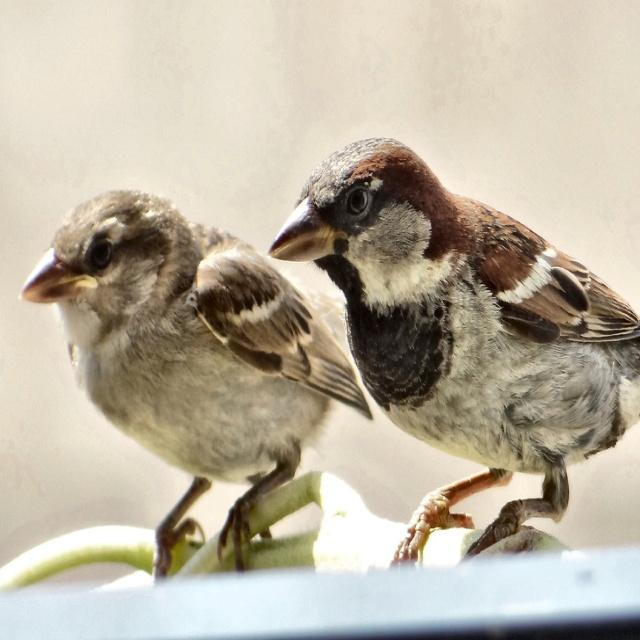
fifth_model_validation_images/images/34544401c4a3e79f_jpg.rf.0eca268f61210abd825abad05dea3782.jpg
