massengineer/FYP-ML-Bird-Scarer/fifth_model_validation_images/images/58211944ca5425aa_jpg.rf.850591d0a5f511dc21ecf8095d111a85.jpg

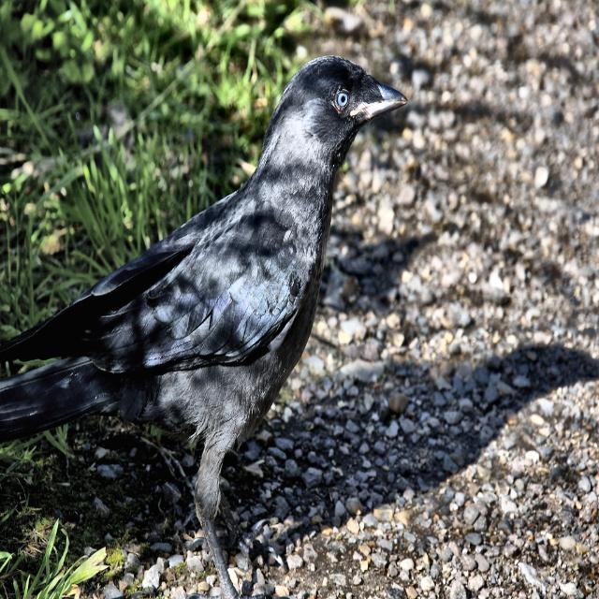
fifth_model_validation_images/images/58211944ca5425aa_jpg.rf.850591d0a5f511dc21ecf8095d111a85.jpg
