massengineer/FYP-ML-Bird-Scarer/fifth_model_validation_images/images/a734347163869934_jpg.rf.759c2eac67e7a64f80a03febb55eb755.jpg

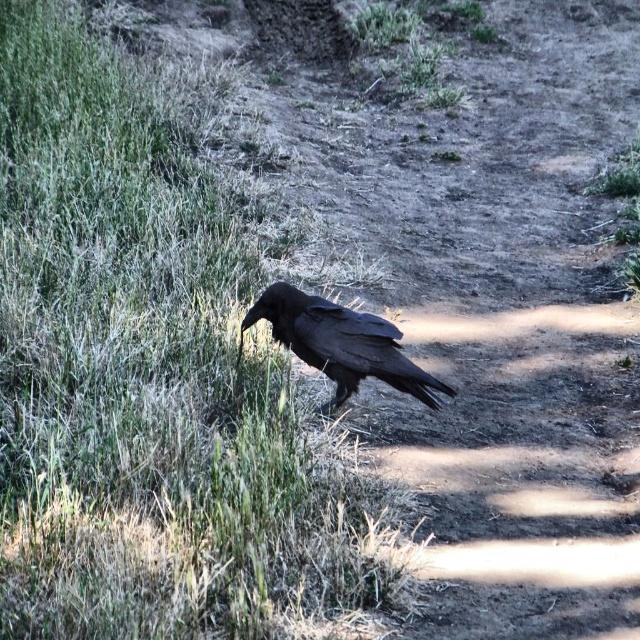
fifth_model_validation_images/images/a734347163869934_jpg.rf.759c2eac67e7a64f80a03febb55eb755.jpg
