massengineer/FYP-ML-Bird-Scarer/fifth_model_validation_images/images/b5341a0c87e7784f_jpg.rf.efdc447a5d2ed24ab40c7e8ae7609804.jpg

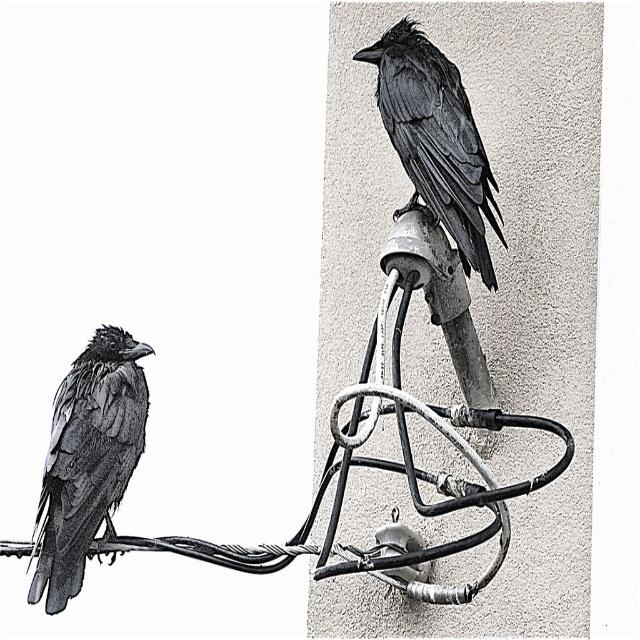
fifth_model_validation_images/images/b5341a0c87e7784f_jpg.rf.efdc447a5d2ed24ab40c7e8ae7609804.jpg
