massengineer/FYP-ML-Bird-Scarer/fifth_model_validation_images/images/be6527c2dfd5fa7d_jpg.rf.3ea14cc2ab2f299e615fa3b19aab1c70.jpg

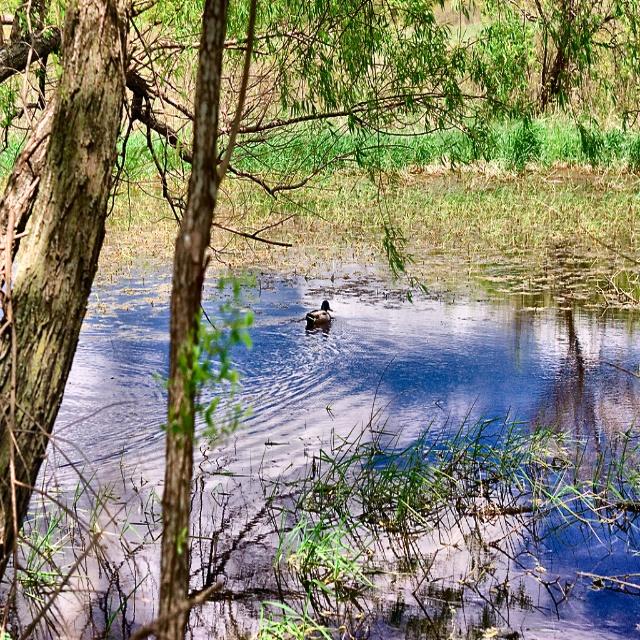
fifth_model_validation_images/images/be6527c2dfd5fa7d_jpg.rf.3ea14cc2ab2f299e615fa3b19aab1c70.jpg
