massengineer/FYP-ML-Bird-Scarer/fifth_model_validation_images/images/c1555b967654d01f_jpg.rf.b73906f9b4d10556ca54060680107165.jpg

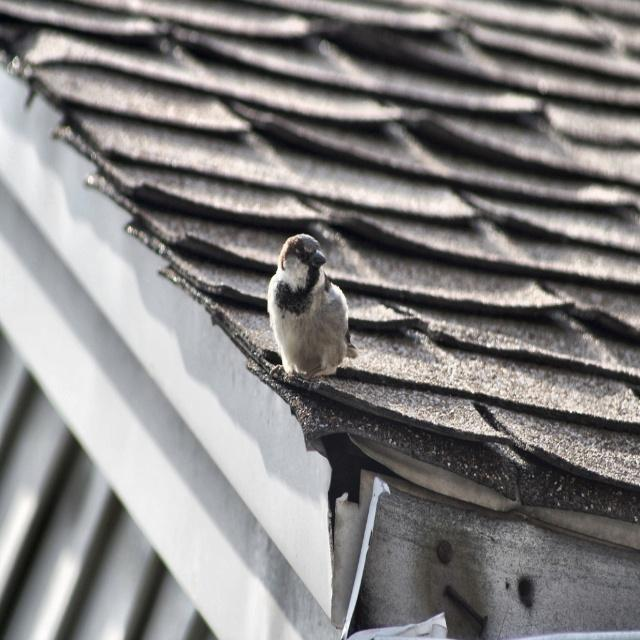
fifth_model_validation_images/images/c1555b967654d01f_jpg.rf.b73906f9b4d10556ca54060680107165.jpg
