massengineer/FYP-ML-Bird-Scarer/fifth_model_validation_images/images/cc2af1caf5f4a36b_jpg.rf.9c7e3c0979db96ce613e024710375188.jpg

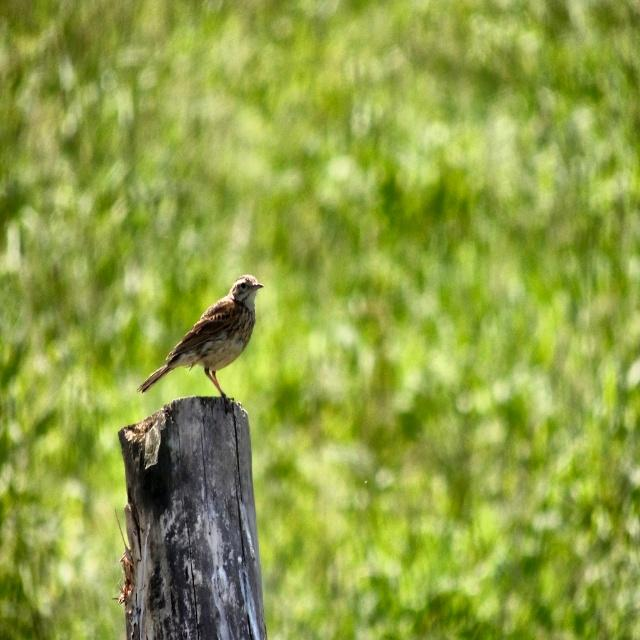
fifth_model_validation_images/images/cc2af1caf5f4a36b_jpg.rf.9c7e3c0979db96ce613e024710375188.jpg
