massengineer/FYP-ML-Bird-Scarer/fifth_model_validation_images/images/cdbe667ec330f223_jpg.rf.fcd20ea5d9674c55a1acb1828a1136ff.jpg

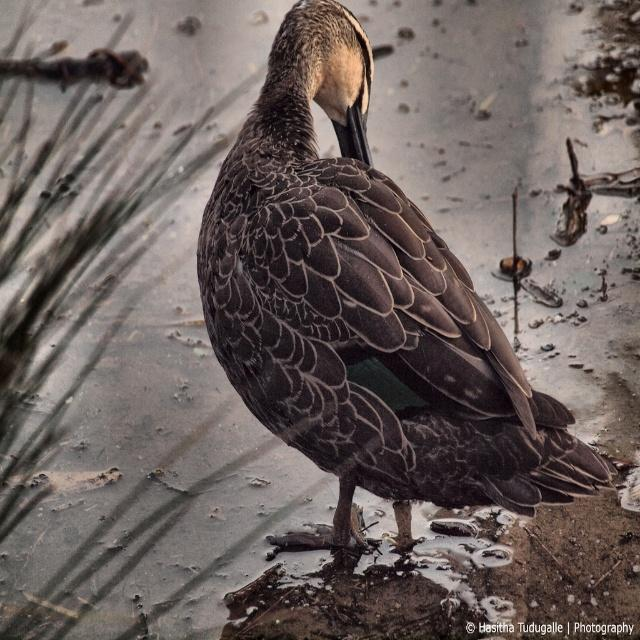
fifth_model_validation_images/images/cdbe667ec330f223_jpg.rf.fcd20ea5d9674c55a1acb1828a1136ff.jpg
