massengineer/FYP-ML-Bird-Scarer/fifth_model_validation_images/images/ce5b7501084b301c_jpg.rf.12cb383f7fdf280a2248405b6c2c0ab6.jpg

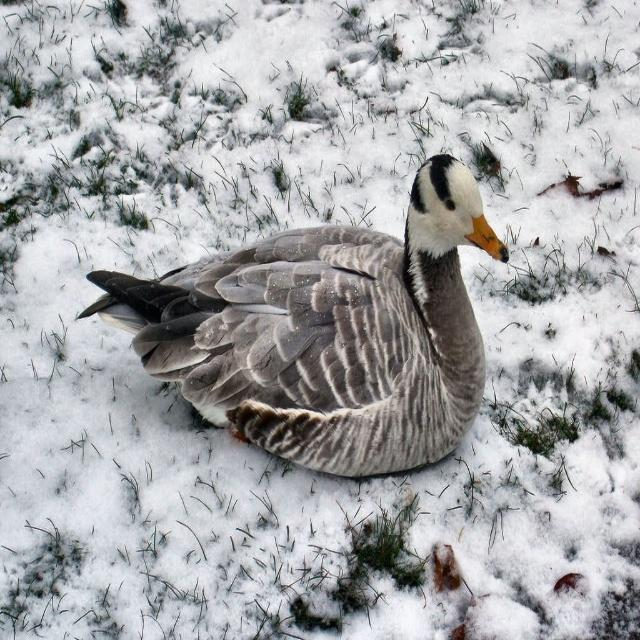
fifth_model_validation_images/images/ce5b7501084b301c_jpg.rf.12cb383f7fdf280a2248405b6c2c0ab6.jpg
