massengineer/FYP-ML-Bird-Scarer/fifth_model_validation_images/images/d1c5e9ba57e89786_jpg.rf.d2ea6ad5fba449561cd475dfe87e4015.jpg

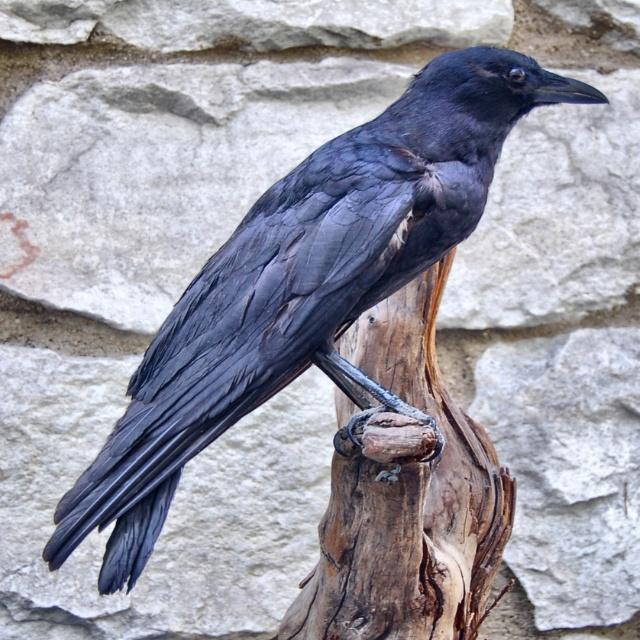
fifth_model_validation_images/images/d1c5e9ba57e89786_jpg.rf.d2ea6ad5fba449561cd475dfe87e4015.jpg
