massengineer/FYP-ML-Bird-Scarer/fifth_model_validation_images/images/d8f41b4ec91b7bea_jpg.rf.341640a5c30362b2a154c29d3c2c68e4.jpg

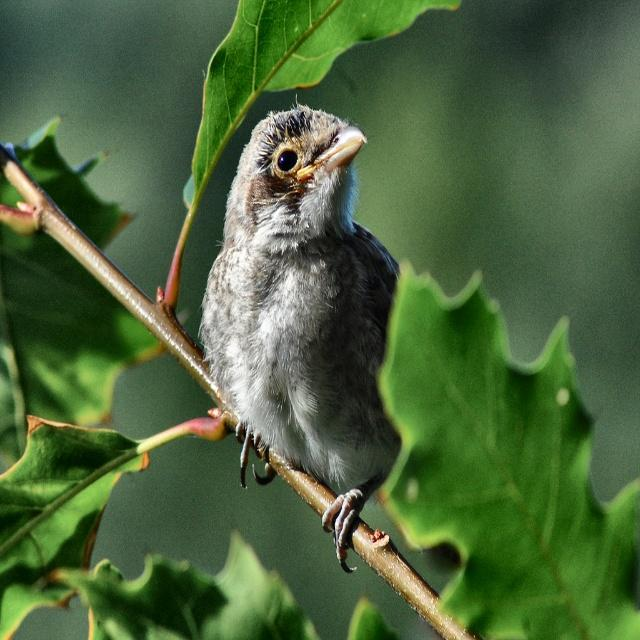
fifth_model_validation_images/images/d8f41b4ec91b7bea_jpg.rf.341640a5c30362b2a154c29d3c2c68e4.jpg
