massengineer/FYP-ML-Bird-Scarer/fifth_model_validation_images/images/d38907bded848276_jpg.rf.cc87c668a2239674f642f8850a6a4cb1.jpg

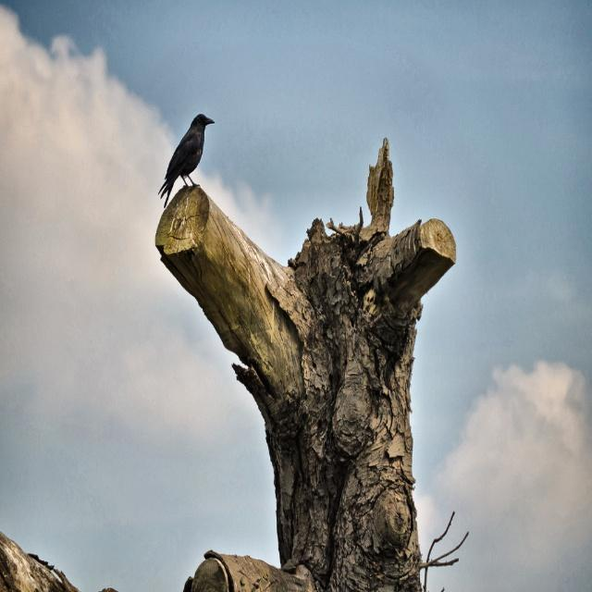
fifth_model_validation_images/images/d38907bded848276_jpg.rf.cc87c668a2239674f642f8850a6a4cb1.jpg
