massengineer/FYP-ML-Bird-Scarer/fifth_model_validation_images/images/e74af19983cce981_jpg.rf.ddab87604cb8b459e48ea78538035e9e.jpg

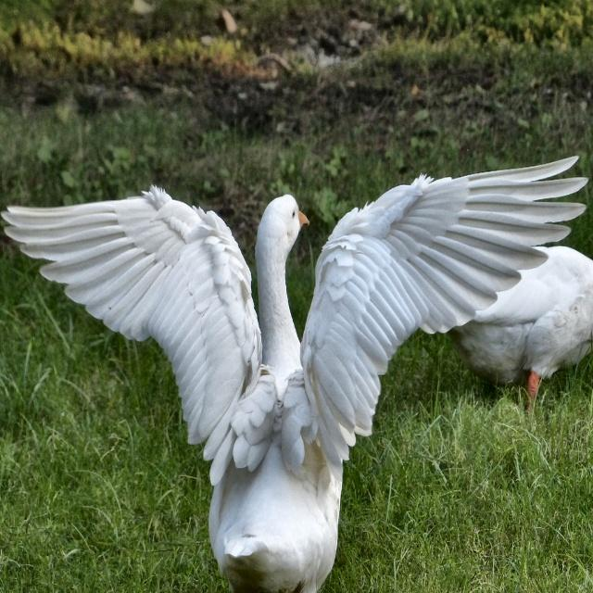
fifth_model_validation_images/images/e74af19983cce981_jpg.rf.ddab87604cb8b459e48ea78538035e9e.jpg
