massengineer/FYP-ML-Bird-Scarer/fifth_model_validation_images/images/eb007a017100c525_jpg.rf.f38cf37cdc9a23c56f058f8f42ee7840.jpg

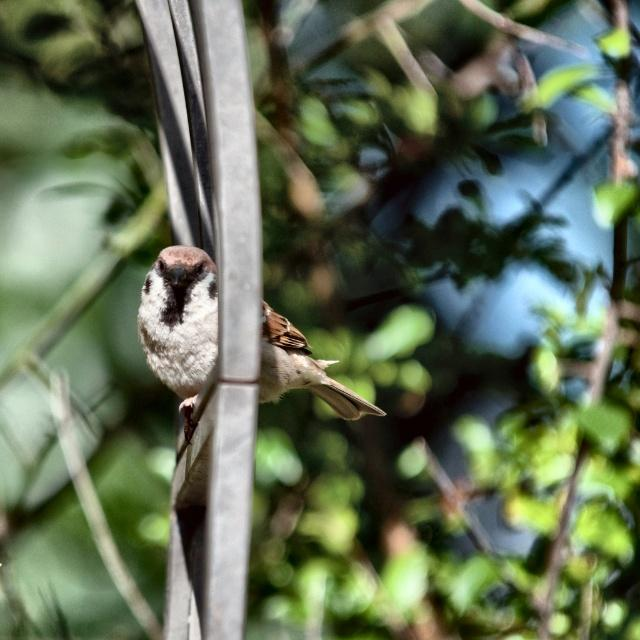
fifth_model_validation_images/images/eb007a017100c525_jpg.rf.f38cf37cdc9a23c56f058f8f42ee7840.jpg
