massengineer/FYP-ML-Bird-Scarer/fifth_model_validation_images/images/edc1658db75333f1_jpg.rf.8f2bbf7bb8b1af6970222284312f2f18.jpg

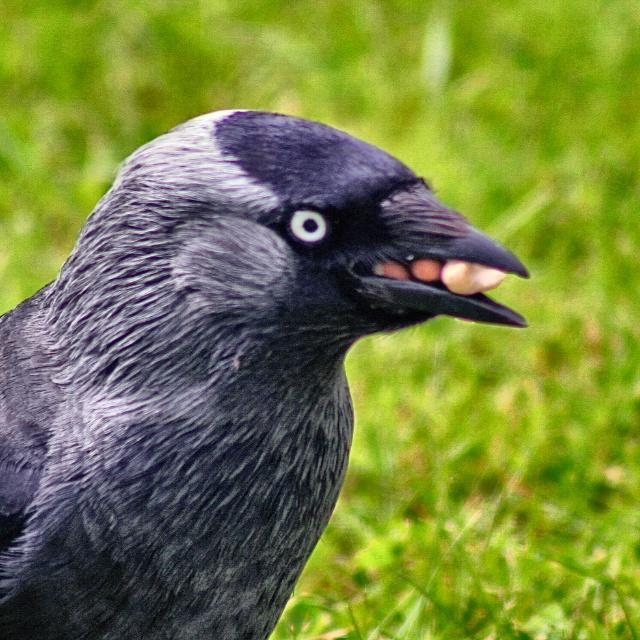
fifth_model_validation_images/images/edc1658db75333f1_jpg.rf.8f2bbf7bb8b1af6970222284312f2f18.jpg
