massengineer/FYP-ML-Bird-Scarer/fifth_model_validation_images/images/f6bef7d891d1b3b1_jpg.rf.6b40b6c9c0b6ad9ba88c7fb941fb4649.jpg

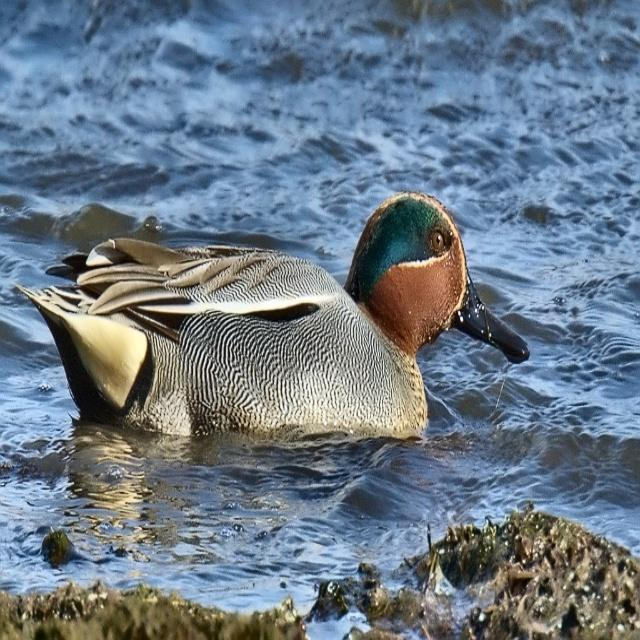
fifth_model_validation_images/images/f6bef7d891d1b3b1_jpg.rf.6b40b6c9c0b6ad9ba88c7fb941fb4649.jpg
