massengineer/FYP-ML-Bird-Scarer/fifth_model_validation_images/images/f9bc5dc66e6d1301_jpg.rf.12b9872e3ca112a5ebb8c23c535df6b4.jpg

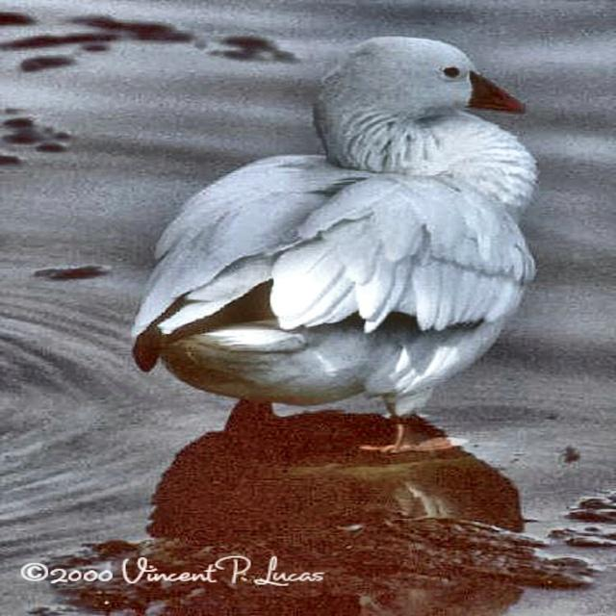
fifth_model_validation_images/images/f9bc5dc66e6d1301_jpg.rf.12b9872e3ca112a5ebb8c23c535df6b4.jpg
