massengineer/FYP-ML-Bird-Scarer/fifth_model_validation_images/images/fcad66e31050b774_jpg.rf.613197887586f042e5d12ee36f3410e6.jpg

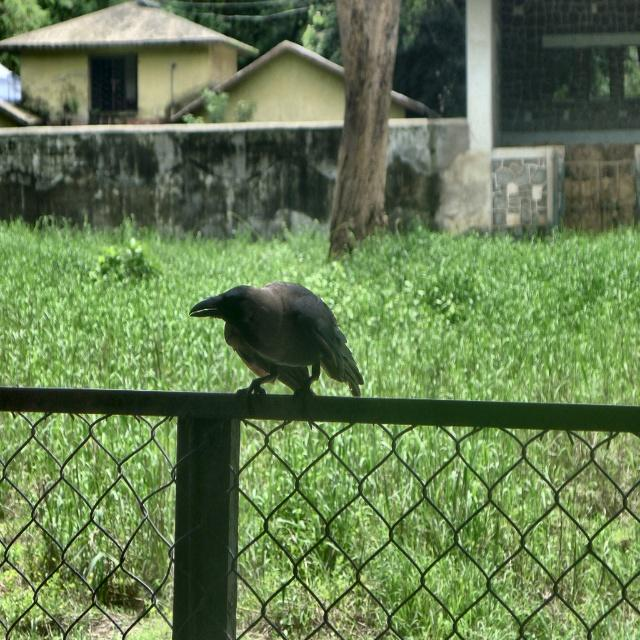
fifth_model_validation_images/images/fcad66e31050b774_jpg.rf.613197887586f042e5d12ee36f3410e6.jpg
