massengineer/FYP-ML-Bird-Scarer/fifth_model_validation_images/images/IMG_20260304_160822_hdr_jpg.rf.aa24e7a804cf44c49cda5c483c167199.jpg

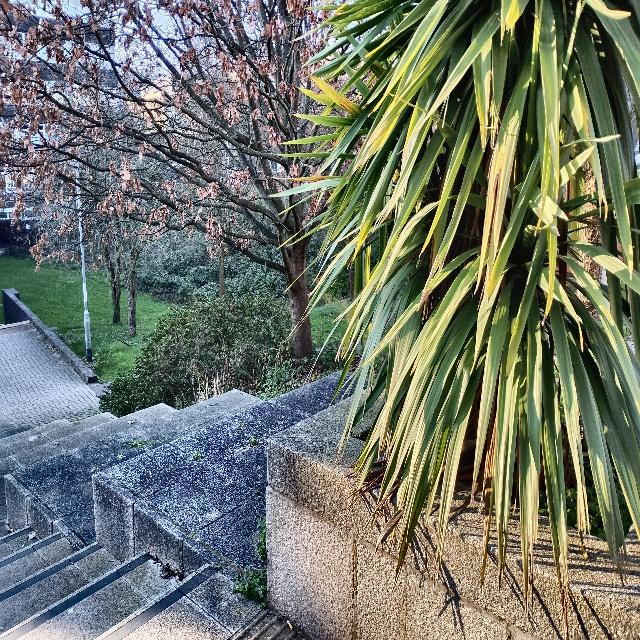
fifth_model_validation_images/images/IMG_20260304_160822_hdr_jpg.rf.aa24e7a804cf44c49cda5c483c167199.jpg
