massengineer/FYP-ML-Bird-Scarer/fifth_model_validation_images/images/IMG_20260304_160844_hdr_jpg.rf.ba1f620c03d966b88cef2f0471ef35ef.jpg

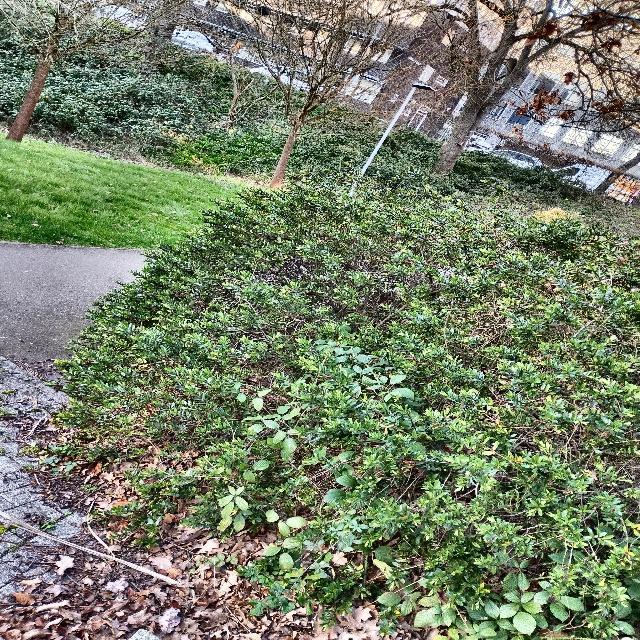
fifth_model_validation_images/images/IMG_20260304_160844_hdr_jpg.rf.ba1f620c03d966b88cef2f0471ef35ef.jpg
