massengineer/FYP-ML-Bird-Scarer/fifth_model_validation_images/images/IMG_20260304_161510_jpg.rf.2d79a9ca88804ecc7a67f8208c187f1b.jpg

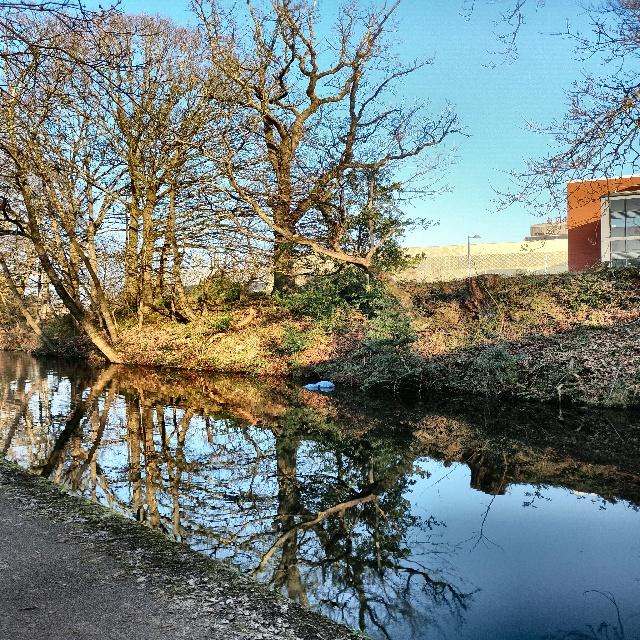
fifth_model_validation_images/images/IMG_20260304_161510_jpg.rf.2d79a9ca88804ecc7a67f8208c187f1b.jpg
