massengineer/FYP-ML-Bird-Scarer/fifth_model_validation_images/images/IMG_20260304_180138_jpg.rf.8b2773d2c4d93c1d0f91aaa077fc2bf7.jpg

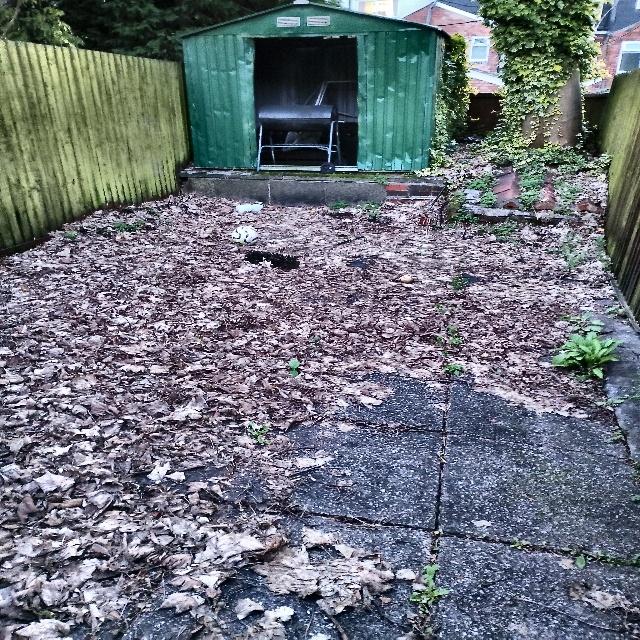
fifth_model_validation_images/images/IMG_20260304_180138_jpg.rf.8b2773d2c4d93c1d0f91aaa077fc2bf7.jpg
