massengineer/FYP-ML-Bird-Scarer/train_data_for_sixth_model/results.png

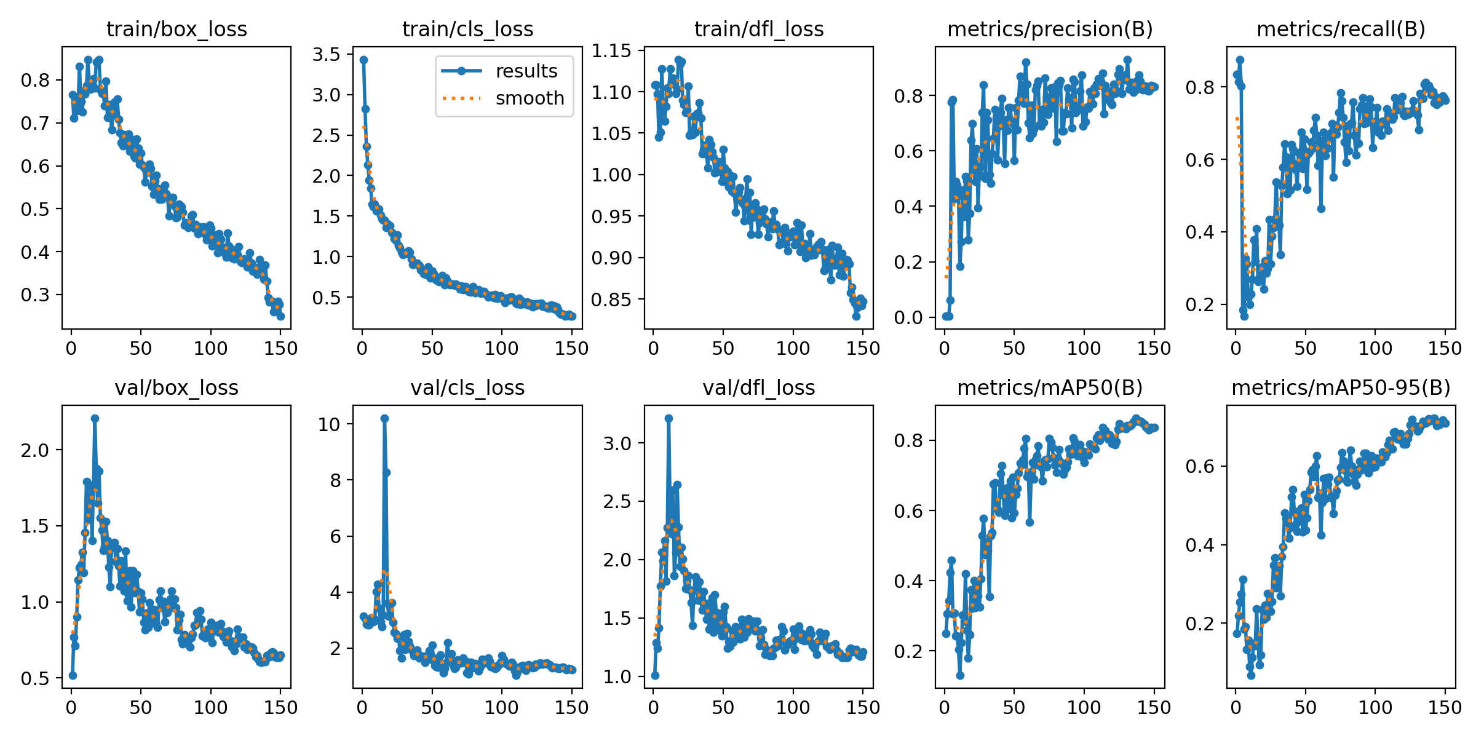
train_data_for_sixth_model/results.png
