massengineer/FYP-ML-Bird-Scarer/tests_and_sandbox/load_env_var_test.py

# importing os module for environment variables
import os

# importing necessary functions from dotenv library
from dotenv import load_dotenv

# loading variables from .env file
load_dotenv()

# accessing and printing value
print(os.getenv("ESP32_MAC_ADDRESS"))
